AESilky/sd-zid/doc/Timing-TGTGO_to_TGT-switch.pdf

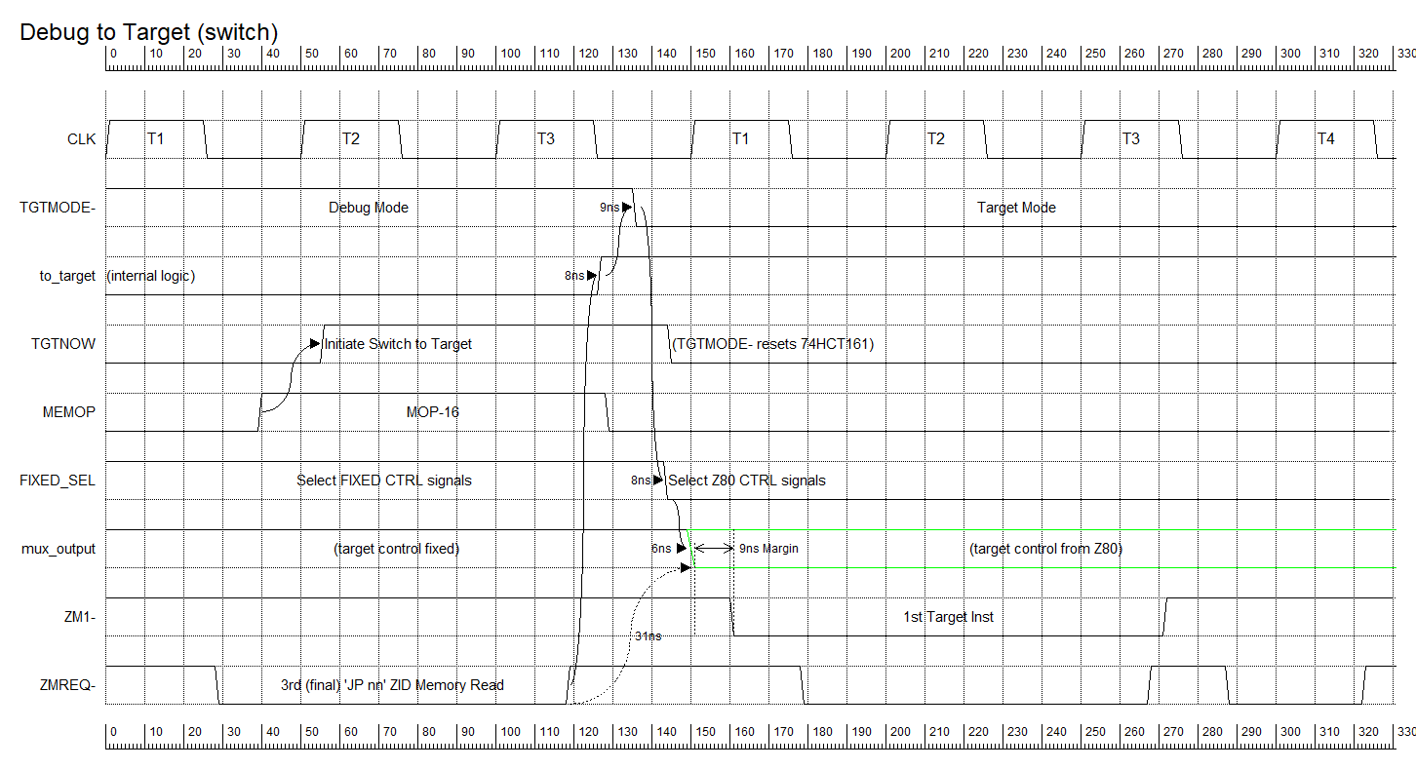
[picture p7: page 1]
