AESilky/sd-zid/doc/Timing-TGTGO_to_TGT-trigger.pdf

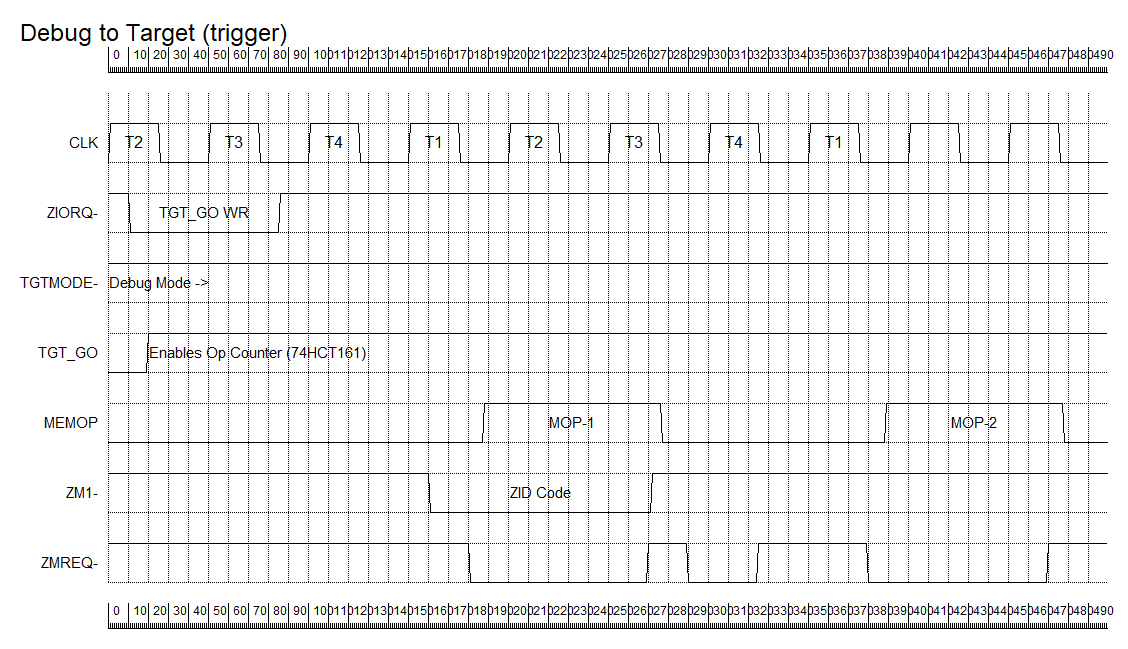
[picture p8: page 1]
