AESilky/sd-zid/doc/ZID-BlockDiag.pdf

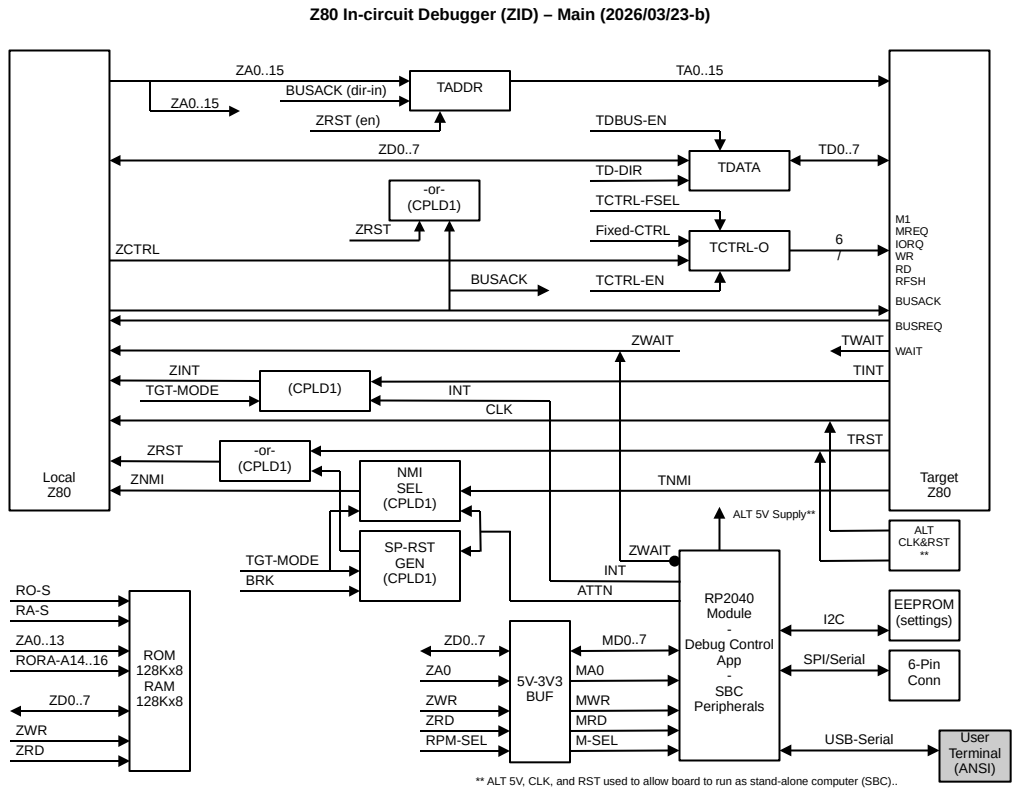
[picture p14: page 1]
User Terminal (ANSI); RP2040 Module - Debug Control App - SBC Peripherals; USB-Serial; EEPROM; (settings); TADDR; TDATA; TCTRL-O; Target Z80; M1 MREQ IORQ WR RD RFSH; Local Z80; SP-RST GEN (CPLD1); NMI SEL (CPLD1); ATTN; ZNMI; TNMI; TRST; -or- (CPLD1); ZRST; (CPLD1); ZINT; TINT; TCTRL-EN; TGT-MODE; ZWAIT; WAIT; RPM-SEL; ALT 5V Supply**; ALT CLK&RST **; BUSACK; BUSREQ; CLK; ROM 128Kx8 RAM; ZA0..13 RORA-A14..16; BRK; Fixed-CTRL; ZCTRL; ZWR ZRD; SPI/Serial; 6-Pin; Conn; INT; TD-DIR; 5V-3V3 BUF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

Z80 In-circuit Debugger (ZID) – Main (2026/03/23-b)

BUSACK (dir-in)

** ALT 5V, CLK, and RST used to allow board to run as stand-alone computer (SBC)..

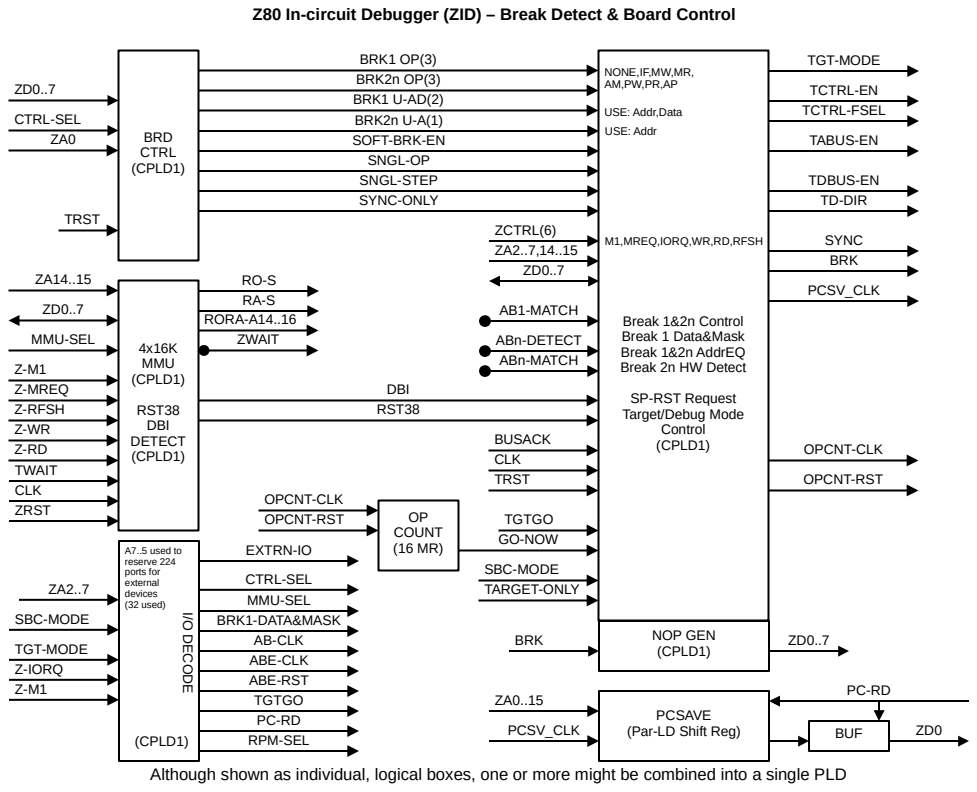
[picture p15: page 2]
ABn-MATCH; BRD CTRL (CPLD1); CTRL-SEL; ZCTRL(6); CLK; OP COUNT (16 MR); TCTRL-FSEL; SYNC; TRST; OPCNT-CLK; OPCNT-RST; OPCNT-CLK OPCNT-RST; GO-NOW; TD-DIR; 4x16K MMU (CPLD1); RST38 DBI DETECT (CPLD1); Z-MREQ; DBI; CLK ZRST; RST38; SBC-MODE; MMU-SEL; BUSACK; TGTGO; ABE-CLK; AB-CLK; ABE-RST TGTGO; Z-IORQ; TGT-MODE; Z-RFSH; RORA-A14..16; BRK; ABn-DETECT; TARGET-ONLY; ZWAIT; NOP GEN (CPLD1); A7..5 used to reserve 224 ports for external devices (32 used); TABUS-EN; TDBUS-EN; PCSV_CLK; AB1-MATCH; BUF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

Z80 In-circuit Debugger (ZID) – Break Detect & Board Control

BRK1 OP(3)
BRK2n OP(3)
BRK1 U-AD(2)
BRK2n U-A(1)
SOFT-BRK-EN
SNGL-OP
SNGL-STEP
SYNC-ONLY

NONE,IF,MW,MR,

USE: Addr,Data
USE: Addr

M1,MREQ,IORQ,WR,RD,RFSH

Break 1&2n Control
Break 1 Data&Mask
Break 1&2n AddrEQ
Break 2n HW Detect

SP-RST Request
Target/Debug Mode
Control
(CPLD1)

RPM-SEL I/O DECODE

PCSAVE
(Par-LD Shift Reg)

Although shown as individual, logical boxes, one or more might be combined into a single PLD

## Break Address Units for

breakpoint-1 and 2-n.

## Target address is shifted into the

AL and AH registers for each unit.

## Address Break Enable is shifted

into ALE and AHE for each unit.

## To detect the number of units present, the Address Break Enables are RESET and a single enable bit is shifted in. After each

2

nd shift, and AB-DETECT is checked. If a unit is detected it is registered and the enable bit is shifted twice, moving it to the next unit. The AB-DETECT is checked again, and if detected, the unit is registered. This process continues until a unit isn’t detected. AB Unit 1 is on the main board, and therefore assumed to exist (no

AB-DETECT needed).

## AB-MATCH and AB-DETECT are Open-Collector outputs to allow all

units to be wire-or’d together.

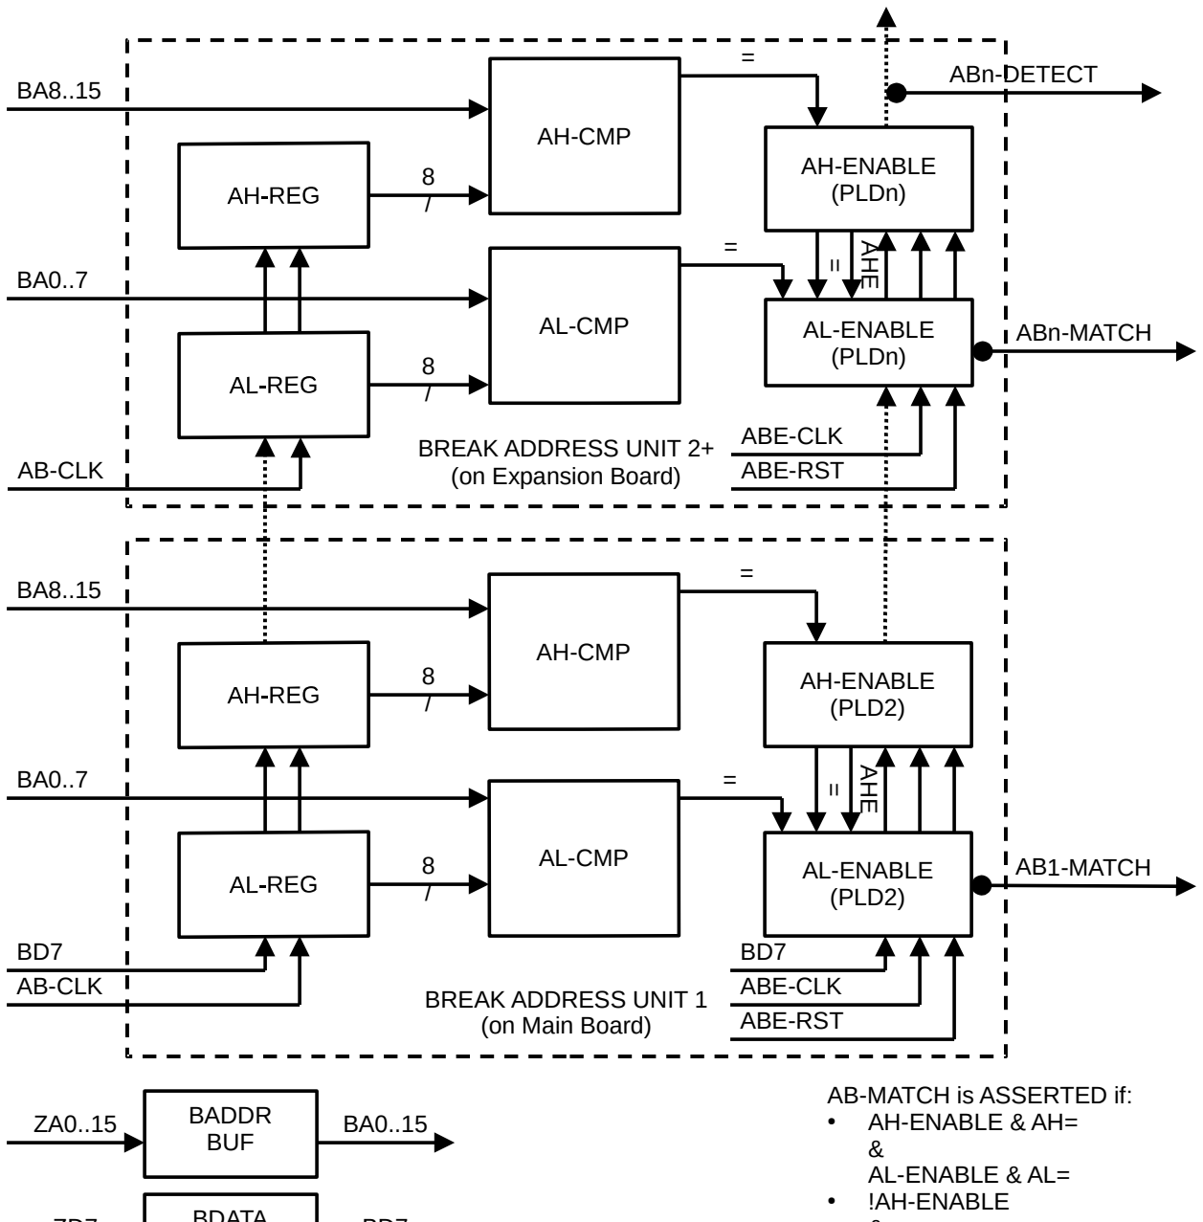
[picture p16: figure]
AL-CMP; AL-ENABLE; (PLD2); BD7 AB-CLK; BD7 ABE-CLK ABE-RST; AH-CMP; AH-ENABLE (PLD2); =AHE; AB1-MATCH; BREAK ADDRESS UNIT 1 (on Main Board); (PLDn) 8 /; AH-ENABLE (PLDn) 8 /; ABn-DETECT; ABn-MATCH; BREAK ADDRESS UNIT 2+ (on Expansion Board); AB-MATCH is ASSERTED if: ● AH-ENABLE & AH= & AL-ENABLE & AL= ● !AH-ENABLE; BA0..15 BADDR BUF; AB-CLK; ABE-CLK ABE-RST

&
AL-ENABLE & AL=

### Z80 In-circuit Debugger (ZID) – Break Address 1 and 2+ Unit(s)

BD7 BDATA
BUF

ZD7
