AESilky/sd-zid/hw/ZID_EXP_BP/schm-plots/ZID_EXP_BP.pdf

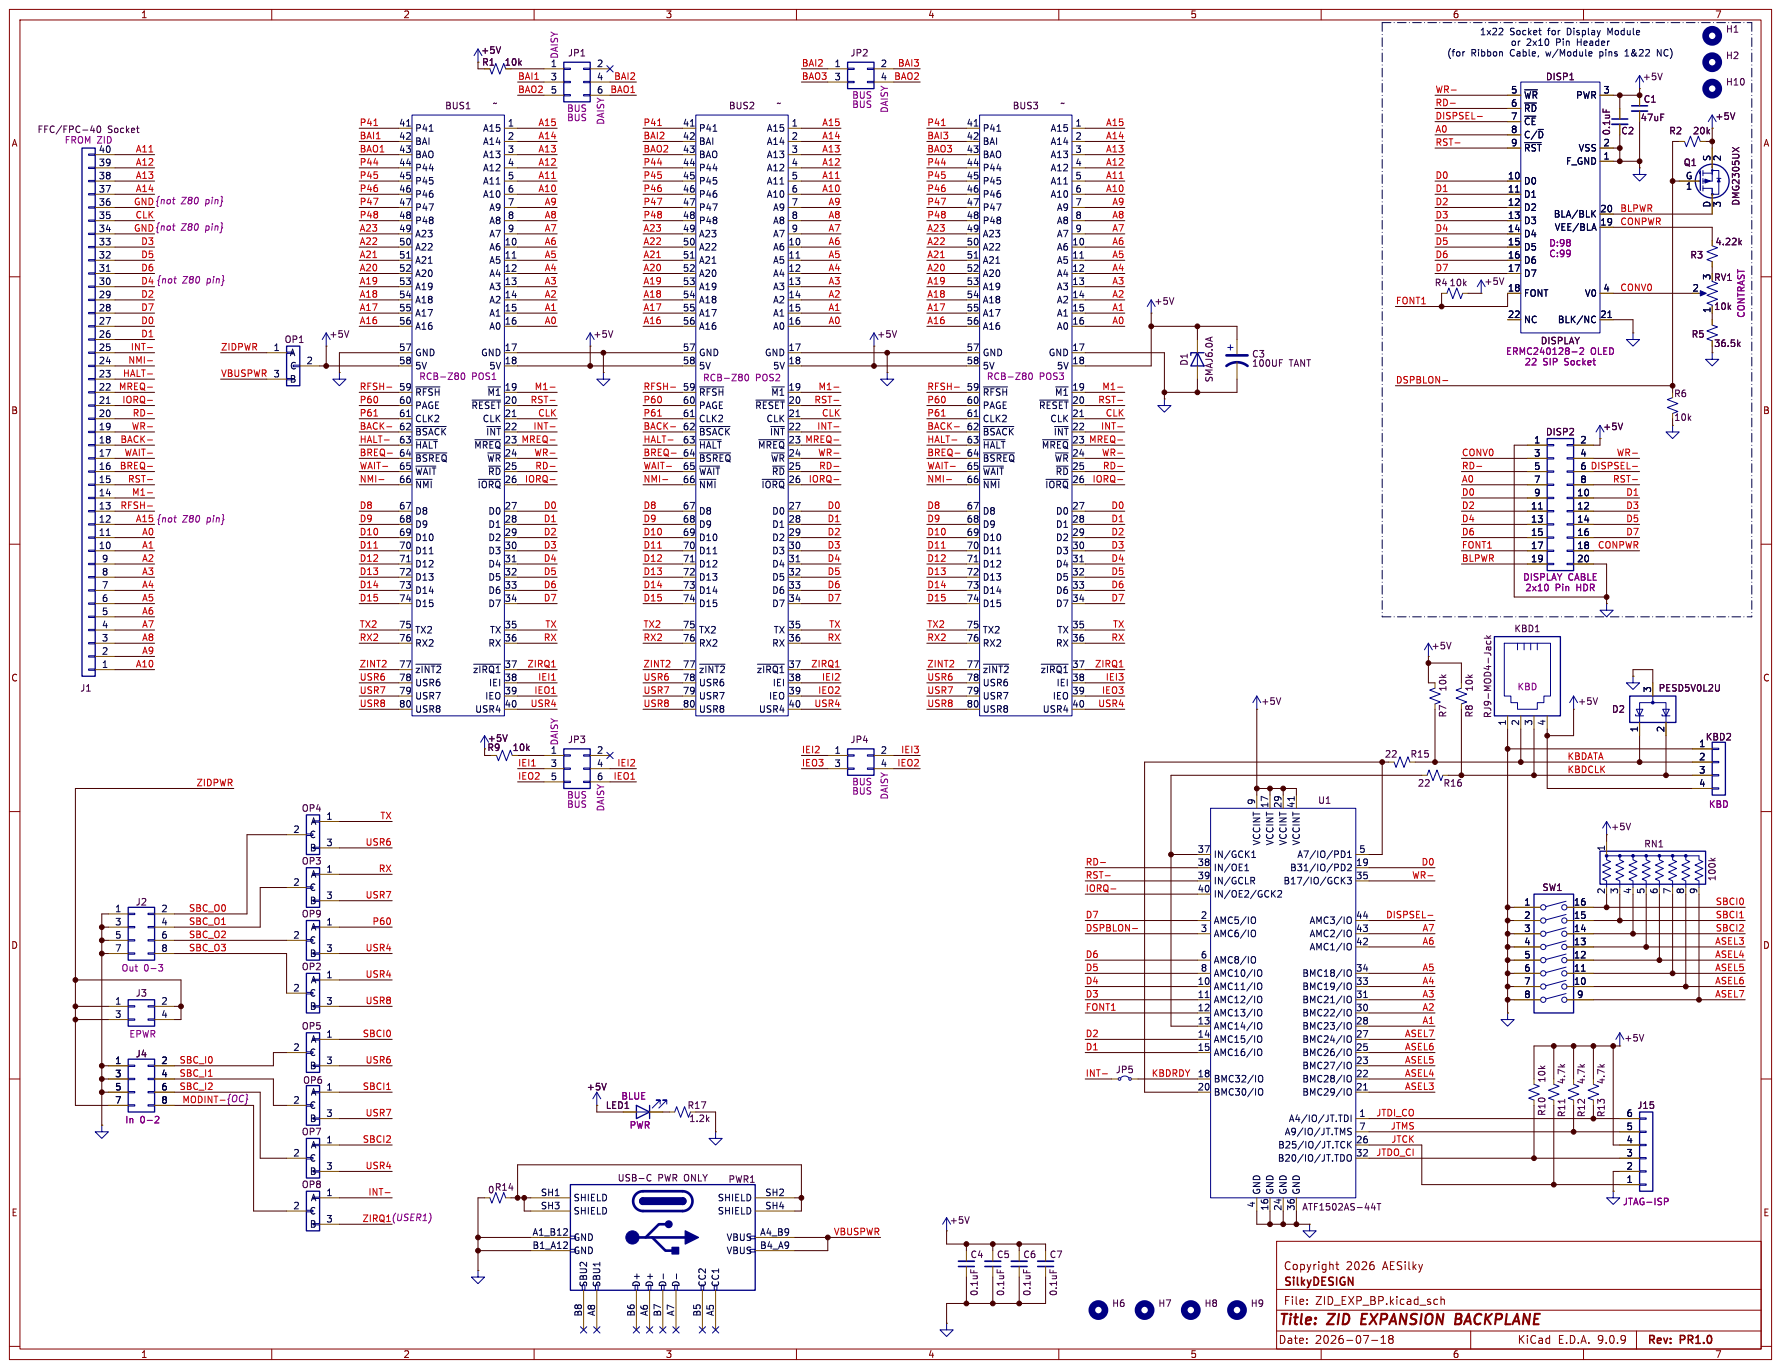
[picture p17: page 1]

1x22 Socket for Display Module
or 2x10 Pin Header
DISP1 DISPLAY

4 VCCINT 17 GND 16 VCCINT 29 GND 24 VCCINT 41 GND 36 A7/IO/PD1 5 B31/IO/PD2 19 B17/IO/GCK3 35 AMC3/IO 44 AMC2/IO 43 AMC1/IO 42 BMC18/IO 34 BMC19/IO 33 BMC21/IO 31 BMC22/IO 30 BMC23/IO 28 BMC24/IO 27 BMC26/IO 25 BMC27/IO 23 BMC28/IO 22 BMC29/IO 21 A4/IO/JT.TDI 1 A9/IO/JT.TMS 7 B25/IO/JT.TCK 26 B20/IO/JT.TDO 32 U1 ATF1502AS-44T 0.1uF C2 C1

A13 GND{not Z80 pin} A14 CLK

5V 58 ~{RFSH} 59 PAGE 60 CLK2 61 ~{BSACK} 62 ~{HALT} 63 ~{BSREQ} 64 ~{WAIT} 65 ~{NMI} 66 D8 67 D9 68 D10 69 D11 70 D12 71 D13 72 D14 73 D15 74 TX2 75 RX2 76 ~{zINT2} 77 USR6 78 USR7 79 USR8 80

5V 18 ~{M1}19 ~{RESET} 20 CLK 21 ~{INT} 22 ~{MREQ} 23 ~{WR} 24 ~{RD} 25 ~{IORQ} 26 D0 27 D1 28 D2 29 D3 30 D4 31 D5 32 D6 33 D7 34 TX 35 RX 36 ~{zIRQ1}37
M1- DSPBLON-
