AESilky/sd-zid/hw/ZID_MAIN/schm-plots/ZID_MAIN.pdf

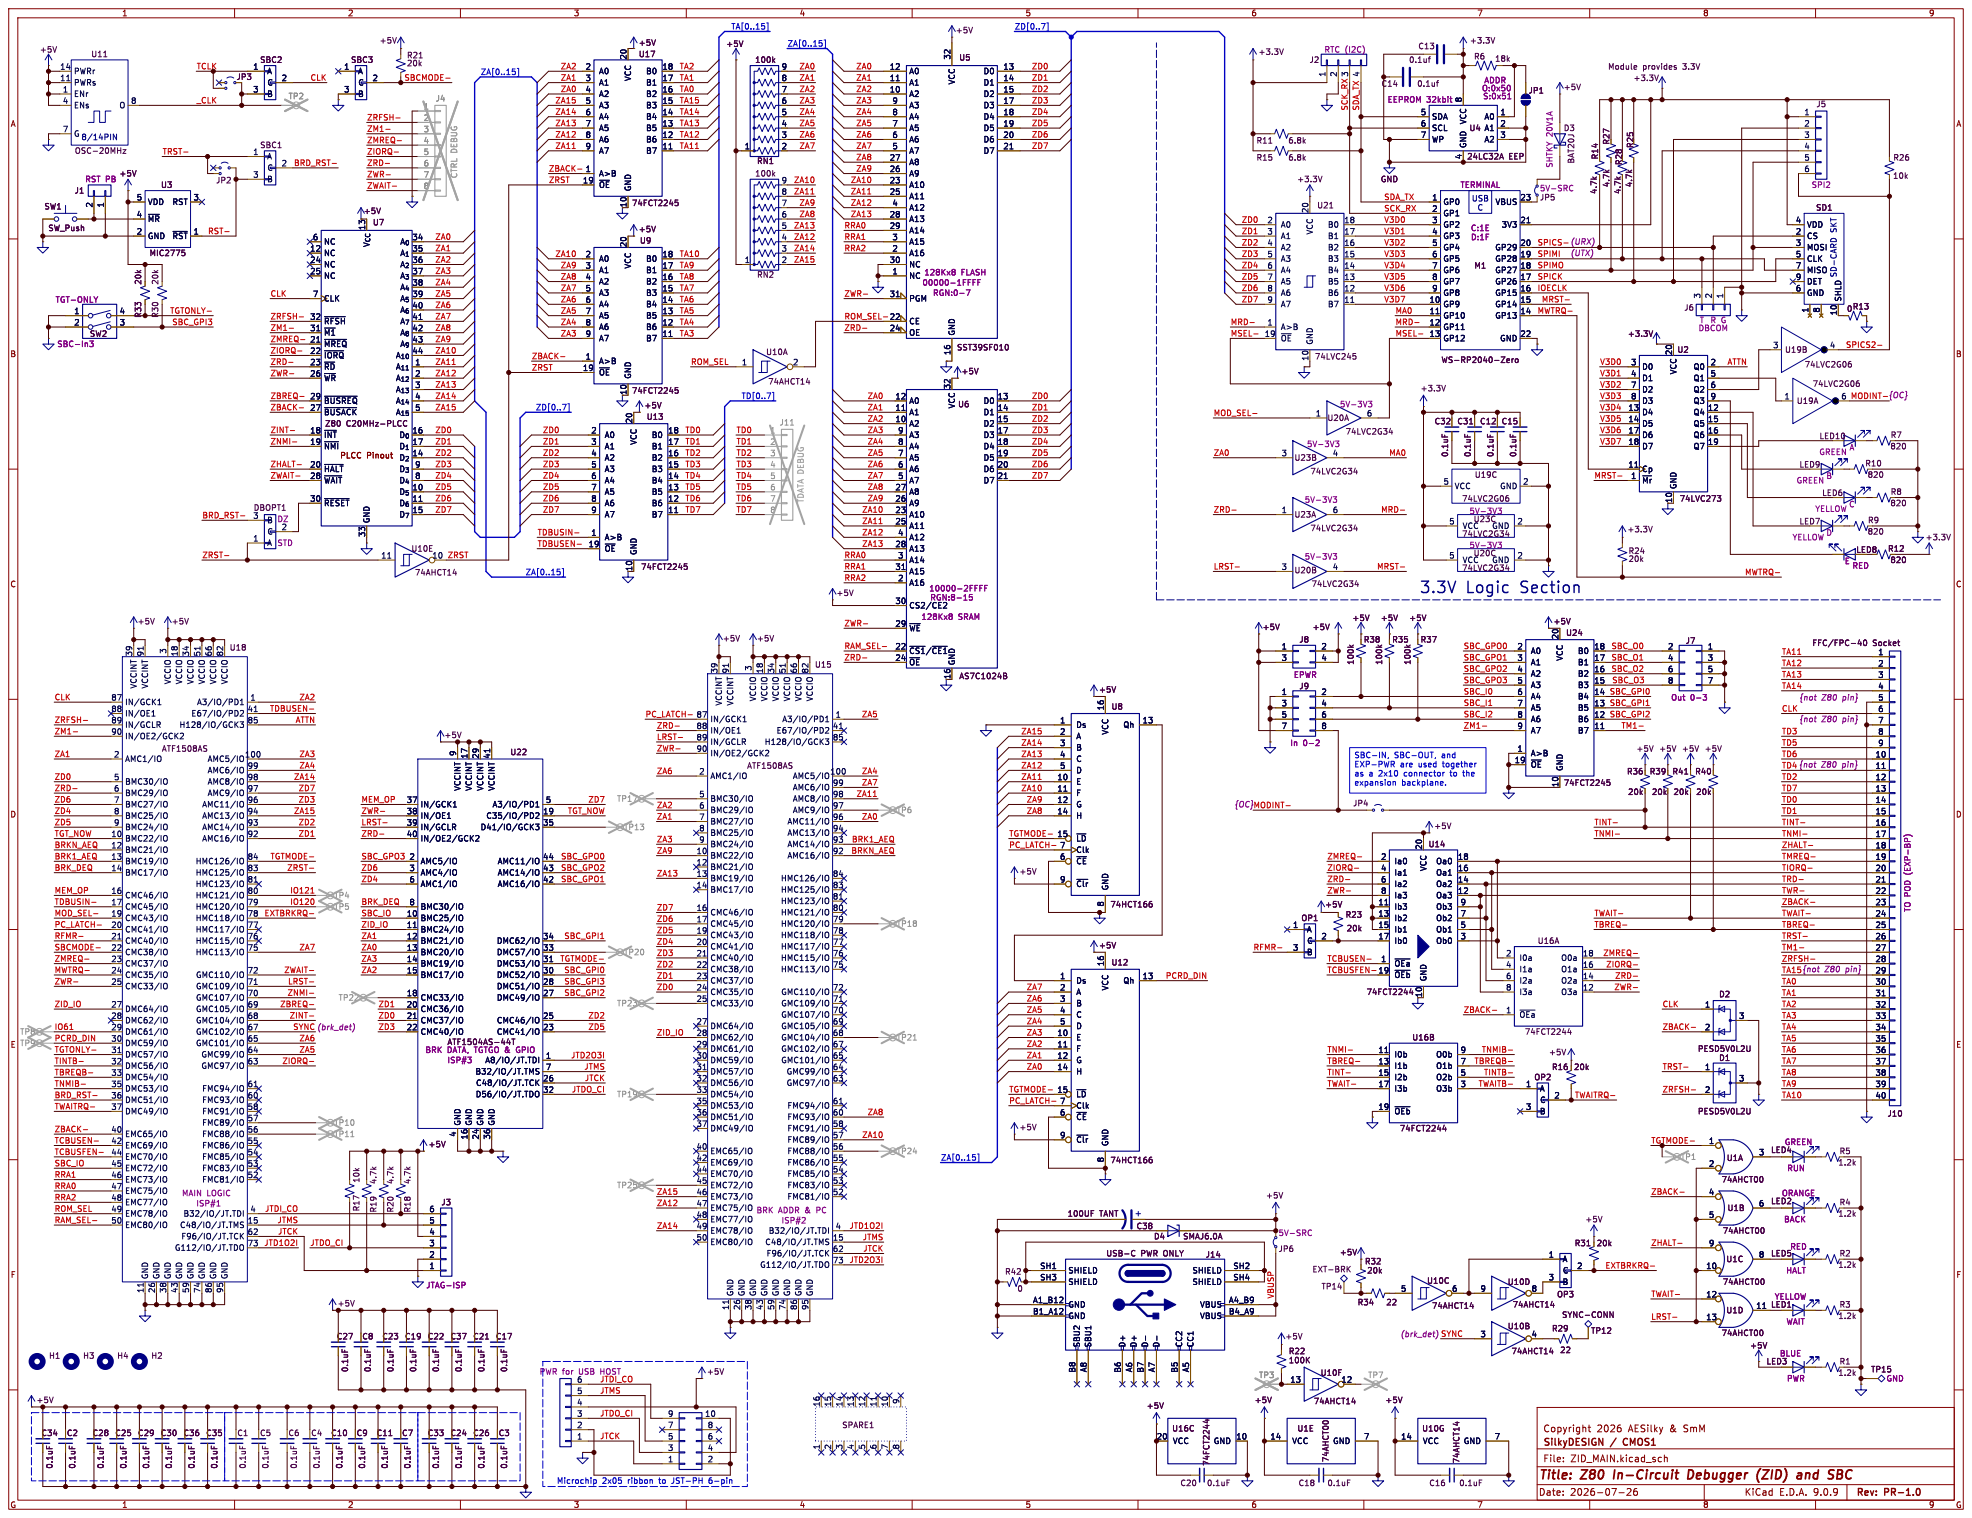
[picture p18: page 1]

Module provides 3.3V 3.3V Logic Section

8 GND
A0 1 A1 2 A2 3 VCC
3V3 21 GP29 20 GP28 19 GP27 18 GP26 17 GP15 16 GP14 15 GP13 14 GND 22 M1 WS-RP2040-Zero TERMINAL C:1E D:1F

4 SDA 5 SCL 6 WP 7 R28 4.7k R25 4.7k R13 0 SD1 VDD

8 SHLD 10 +3.3V M1 WS-RP2040-Zero TERMINAL C:1E D:1F GP0 1 GP1 2 GP2 3 GP3 4 GP4 5 GP5 6 GP6 7 GP7 8 GP8 9 GP9 10 GP10 11 GP11 12 GP12 13 VBUS 23

3 GND 38 VCCIO 18 GND 43 VCCIO 34 GND 59 VCCIO 51 GND 74 VCCIO 66 GND 86 VCCIO 82 GND 95 A3/IO/PD1 1 E67/IO/PD2 41 H128/IO/GCK3 85 AMC5/IO 100 AMC6/IO 99 AMC8/IO 98 AMC9/IO 97 AMC11/IO 96 AMC13/IO 94 AMC14/IO 93 AMC16/IO 92 HMC126/IO 84 HMC125/IO 83 HMC123/IO 81 HMC121/IO 80 HMC120/IO 79 HMC118/IO 78 HMC117/IO 77 HMC115/IO 76 HMC113/IO 75 GMC110/IO 72 GMC109/IO 71 GMC107/IO 70 GMC105/IO 69 GMC104/IO 68 GMC102/IO 67 GMC101/IO 65 GMC99/IO 64 GMC97/IO 63 FMC94/IO 61 FMC93/IO 60 FMC91/IO 58 FMC89/IO 57 FMC88/IO 56 FMC86/IO 55 FMC85/IO 54 FMC83/IO 53 FMC81/IO 52 B32/IO/JT.TDI 4 C48/IO/JT.TMS 15 F96/IO/JT.TCK 62 G112/IO/JT.TDO 73

4 VCCINT 17 GND 16 VCCINT 29 GND 24 VCCINT 41 GND 36 A3/IO/PD1 5 C35/IO/PD2 19 D41/IO/GCK3 35 AMC11/IO 44 AMC14/IO 43 AMC16/IO 42 DMC62/IO 34 DMC57/IO 33 DMC53/IO 31 DMC52/IO 30 DMC51/IO 28 DMC49/IO 27 CMC46/IO 25 CMC41/IO 23 A8/IO/JT.TDI 1 B32/IO/JT.TMS 7 C48/IO/JT.TCK 26 D56/IO/JT.TDO 32 U22 ATF1504AS-44T BRK DATA, TGTGO & GPIO

4 VCCINT 17 GND 16 VCCINT 29 GND 24 VCCINT 41 GND 36 A3/IO/PD1 5 C35/IO/PD2 19 D41/IO/GCK3 35 AMC11/IO 44 AMC14/IO 43 AMC16/IO 42 DMC62/IO 34 DMC57/IO 33 DMC53/IO 31 DMC52/IO 30 DMC51/IO 28 DMC49/IO 27 CMC46/IO 25 CMC41/IO 23 A8/IO/JT.TDI 1 B32/IO/JT.TMS 7 C48/IO/JT.TCK 26 D56/IO/JT.TDO 32 R36

6 PWR for USB HOST
