AESilky/sd-zid/hw/ZID_EXP_BP/comp-docs/Modular_4_Jack-fci-68897-001lf.pdf

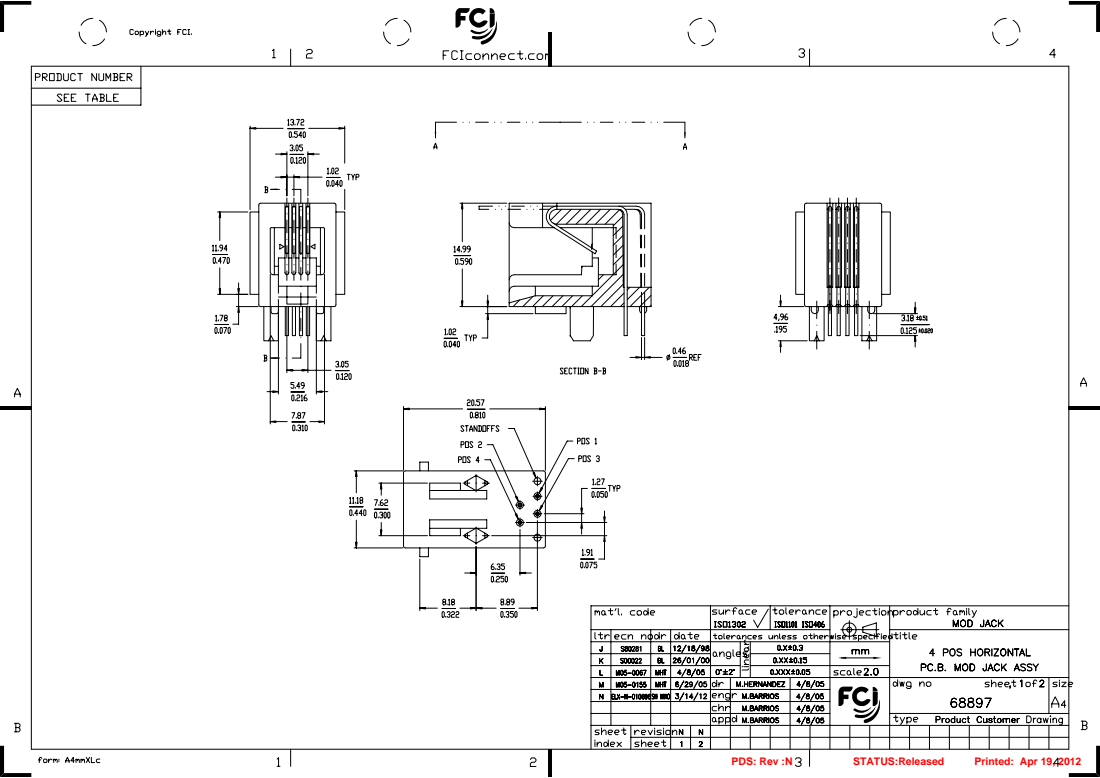
[picture p19: page 1]
PDS: Rev :N; STATUS:Released; Printed: Apr 19, 2012

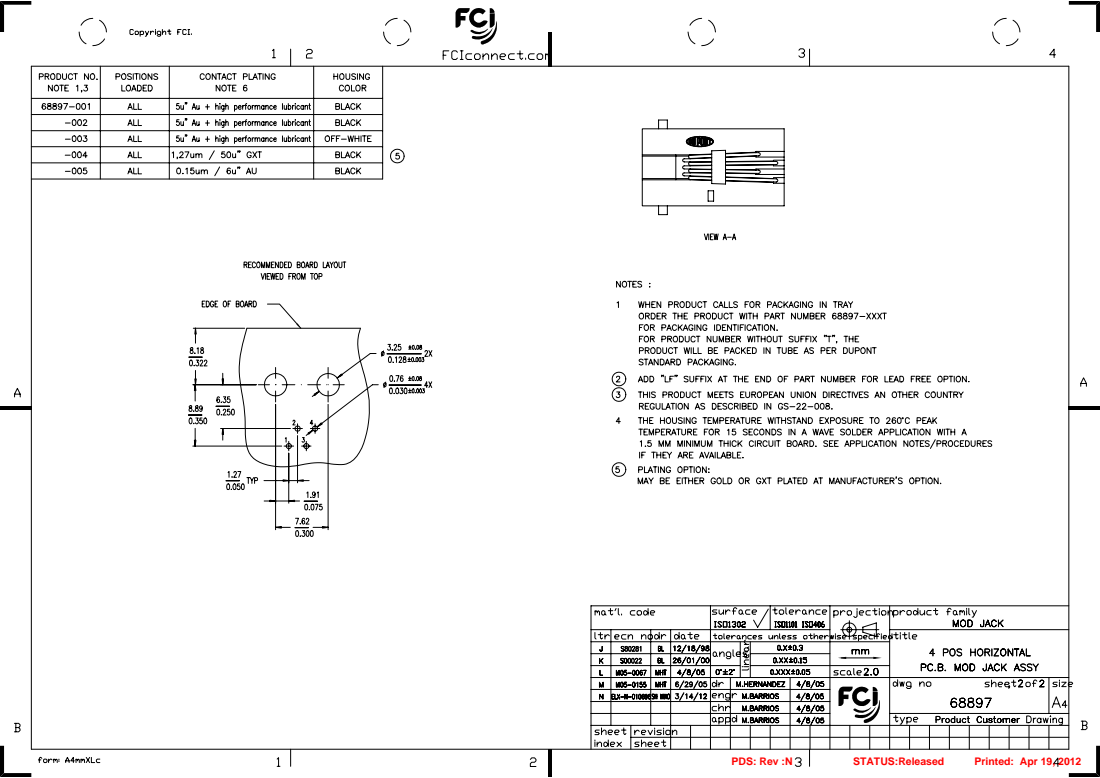
[picture p20: page 2]
PDS: Rev :N; STATUS:Released; Printed: Apr 19, 2012
