AESilky/sd-zid/hw/ZID_BRK_EXP/schm_plots/ZID_BRK_EXP.pdf

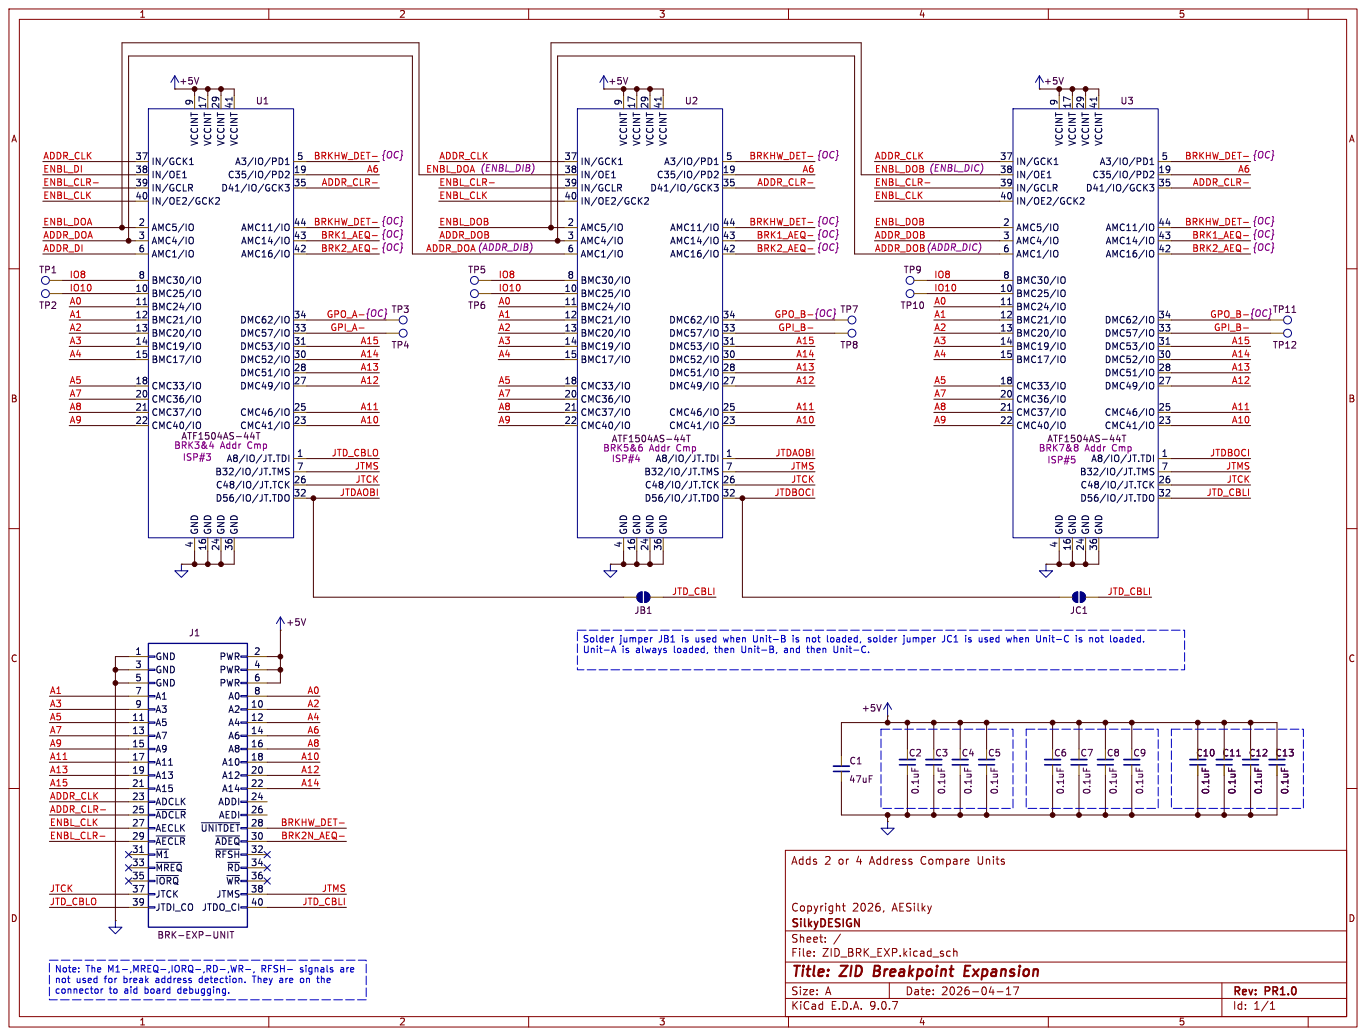
[picture p21: page 1]

4 VCCINT 17 GND 16 VCCINT 29 GND 24 VCCINT 41 GND 36 A3/IO/PD1 5 C35/IO/PD2 19 D41/IO/GCK3 35 AMC11/IO 44 AMC14/IO 43 AMC16/IO 42 DMC62/IO 34 DMC57/IO 33 DMC53/IO 31 DMC52/IO 30 DMC51/IO 28 DMC49/IO 27 CMC46/IO 25 CMC41/IO 23 A8/IO/JT.TDI 1 B32/IO/JT.TMS 7 C48/IO/JT.TCK 26 D56/IO/JT.TDO 32 U1 ATF1504AS-44T BRK3&4 Addr Cmp

4 VCCINT 17 GND 16 VCCINT 29 GND 24 VCCINT 41 GND 36 A3/IO/PD1 5 C35/IO/PD2 19 D41/IO/GCK3 35 AMC11/IO 44 AMC14/IO 43 AMC16/IO 42 DMC62/IO 34 DMC57/IO 33 DMC53/IO 31 DMC52/IO 30 DMC51/IO 28 DMC49/IO 27 CMC46/IO 25 CMC41/IO 23 A8/IO/JT.TDI 1 B32/IO/JT.TMS 7 C48/IO/JT.TCK 26 D56/IO/JT.TDO 32 U2 ATF1504AS-44T BRK5&6 Addr Cmp

4 VCCINT 17 GND 16 VCCINT 29 GND 24 VCCINT 41 GND 36 A3/IO/PD1 5 C35/IO/PD2 19 D41/IO/GCK3 35 AMC11/IO 44 AMC14/IO 43 AMC16/IO 42 DMC62/IO 34 DMC57/IO 33 DMC53/IO 31 DMC52/IO 30 DMC51/IO 28 DMC49/IO 27 CMC46/IO 25 CMC41/IO 23 A8/IO/JT.TDI 1 B32/IO/JT.TMS 7 C48/IO/JT.TCK 26 D56/IO/JT.TDO 32 U3 ATF1504AS-44T BRK7&8 Addr Cmp

Id: 1/1 Title: ZID Breakpoint Expansion
