AESilky/sd-zid/hw/ZID_POD/Pod1/schm-plots/ZID_POD.pdf

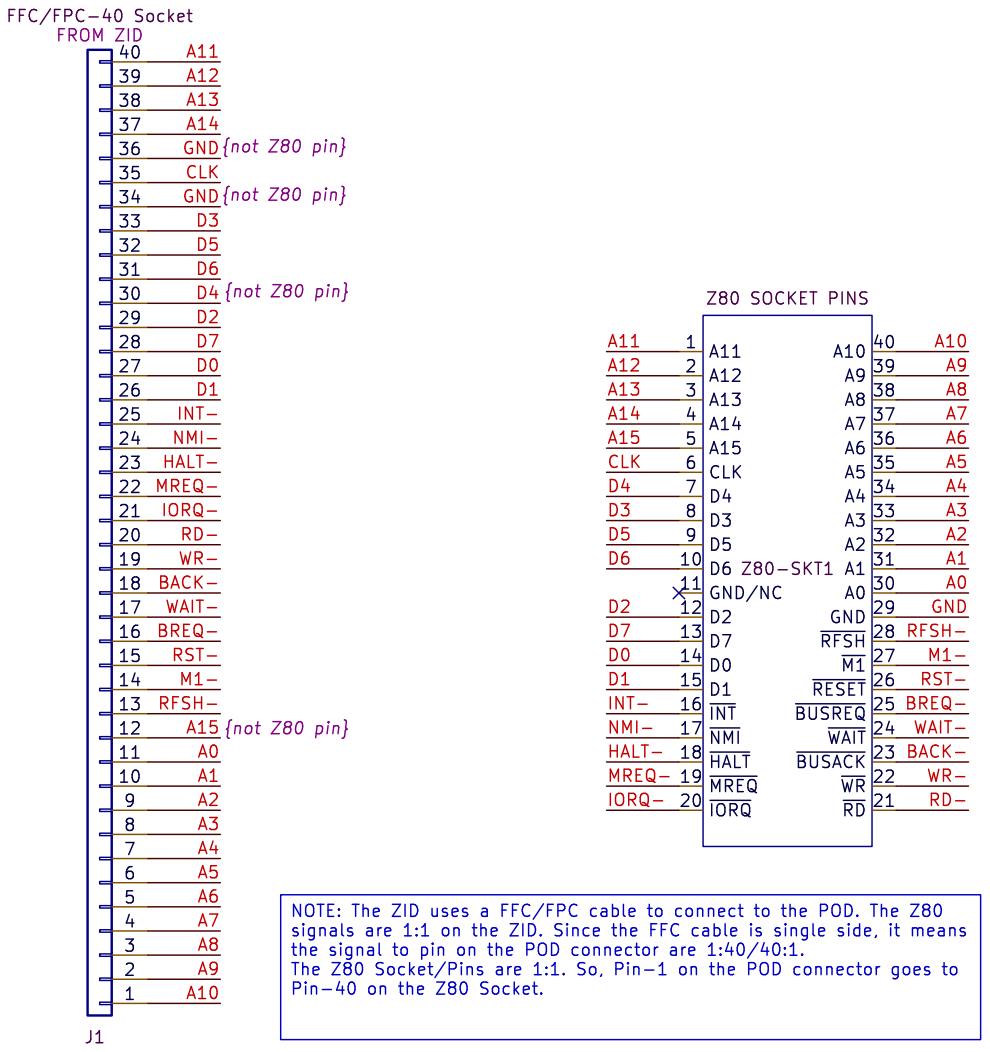
[picture p22: page 1]

INT- MREQ- HALT- NMI- A2A0 A15 {not Z80 pin} A1 A10A7A9A6 RD-A8A4A3 GND{not Z80 pin} CLK

signals are 1:1 on the ZID. Since the FFC cable is single side, it means

Id: 1/1 Title: ZID POD (1) File: ZID_POD.kicad_sch Sheet: / SilkyDESIGN
