AESilky/sd-zid/hw/prod-doc/plcc_44_at_socket.pdf

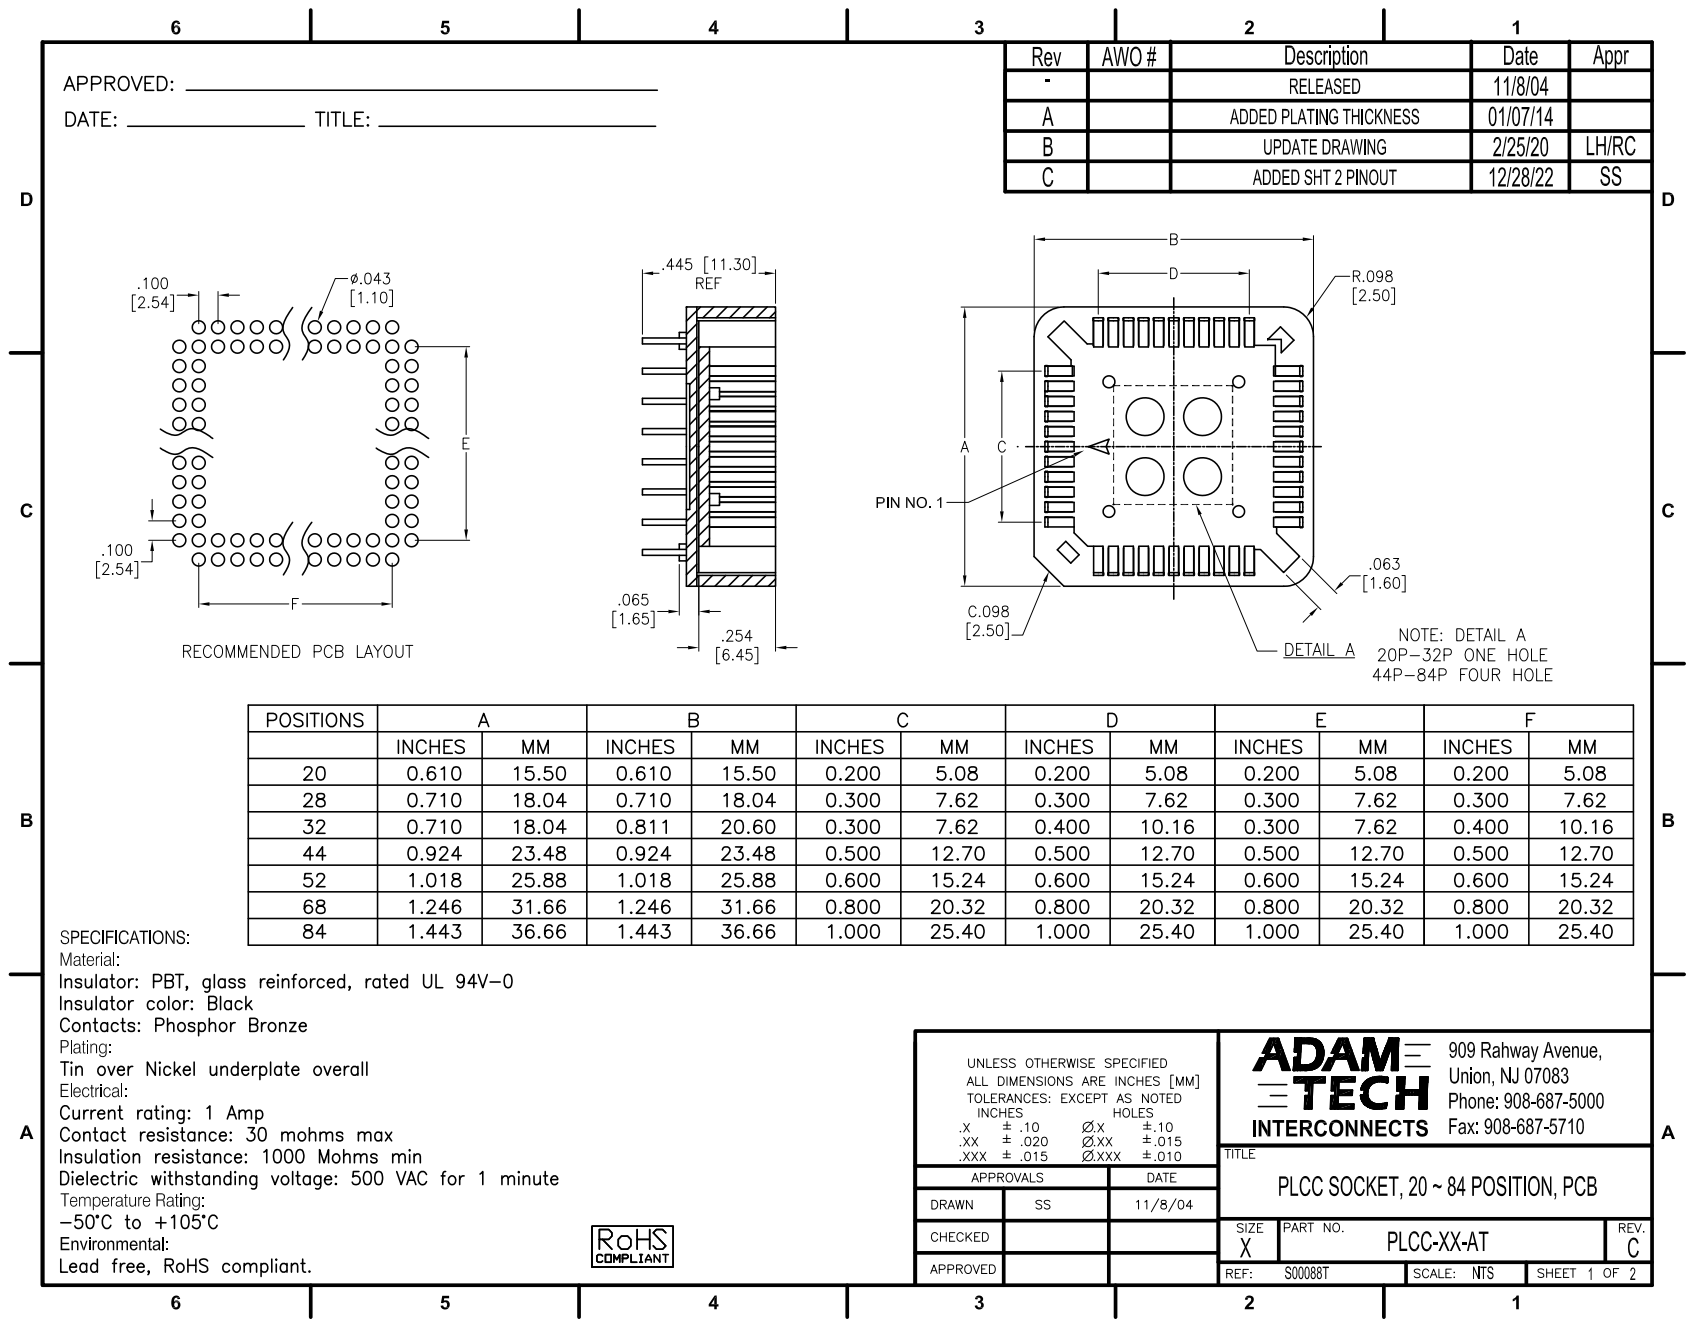
[picture p28: page 1]

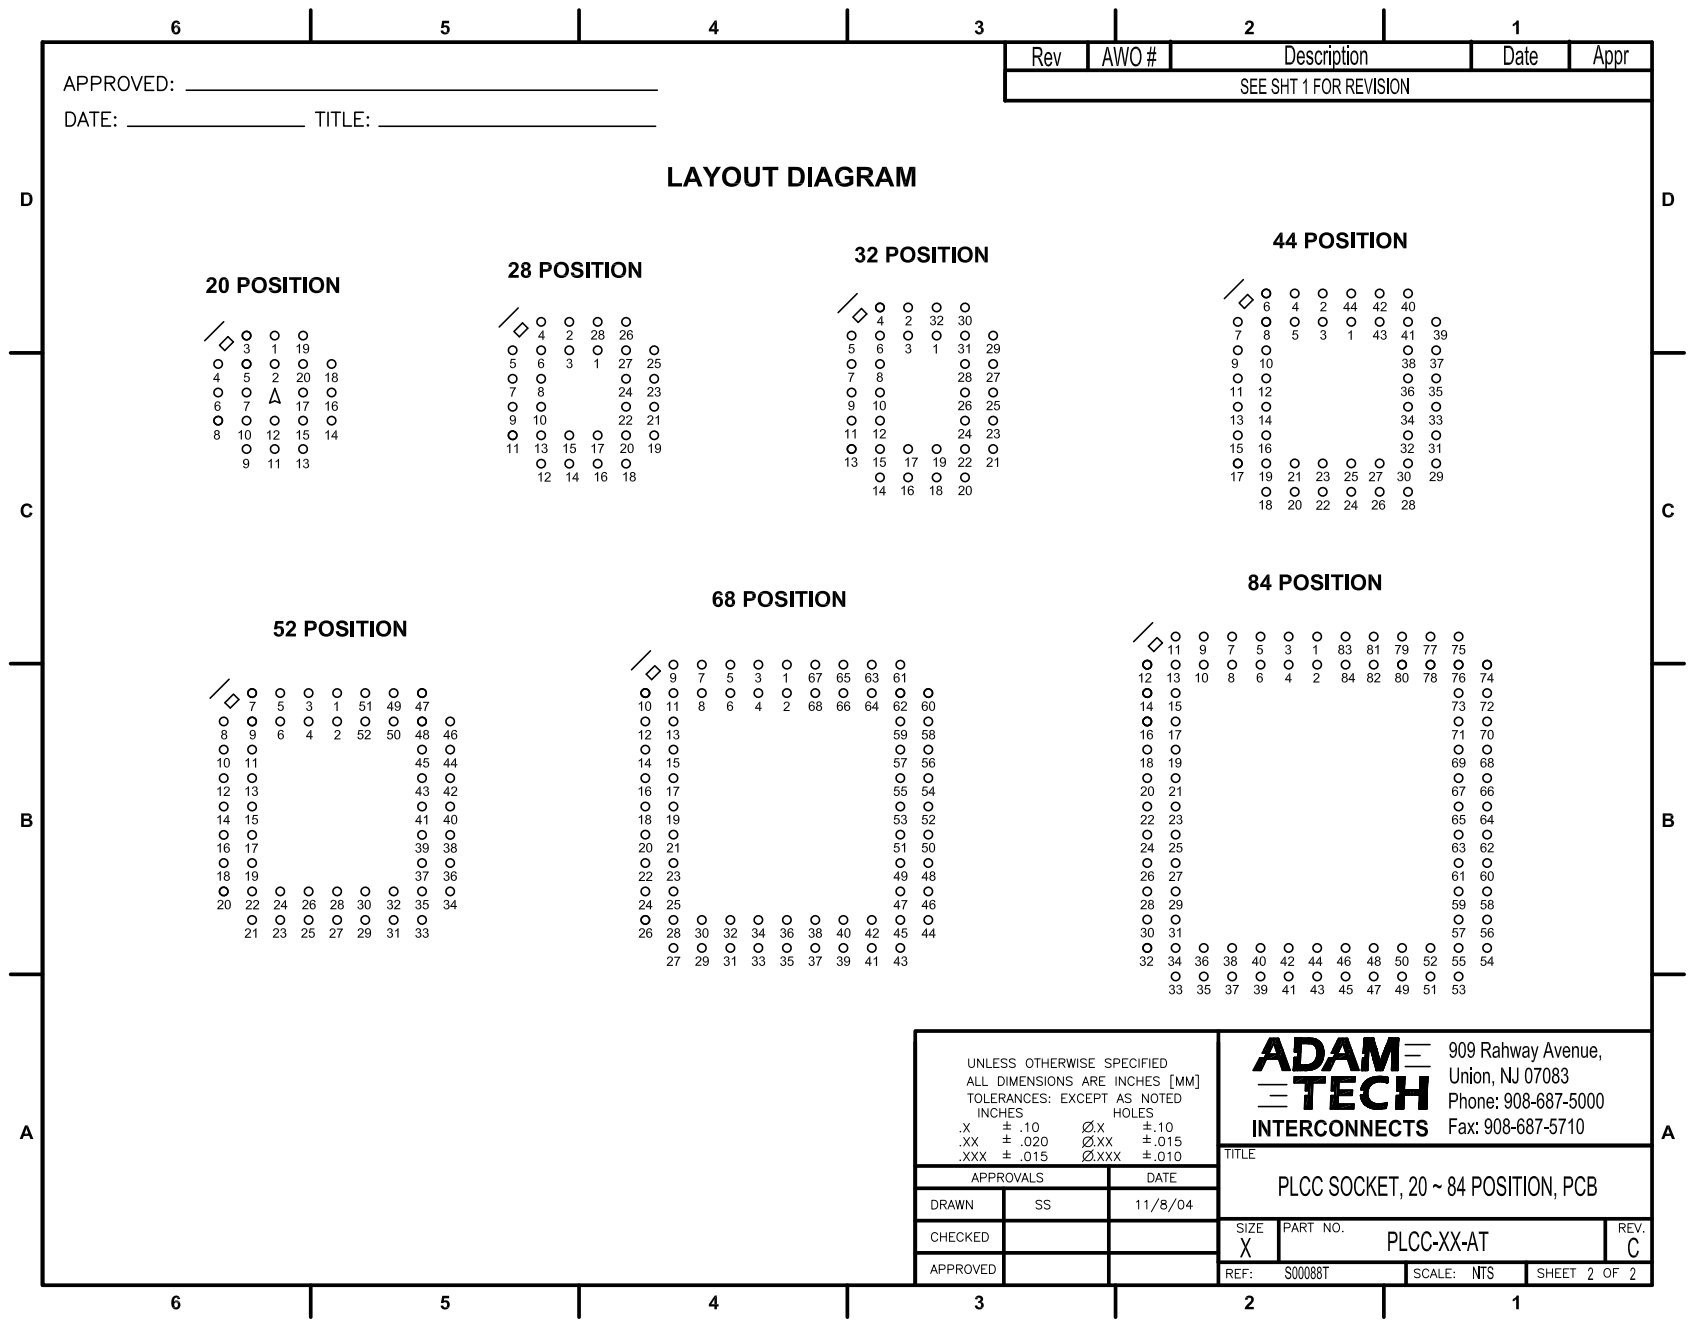
[picture p29: page 2]
