AESilky/sd-zid/hw/prod-doc/FPC-V-Conn-CviLux_CF2081S.pdf

# CviLux

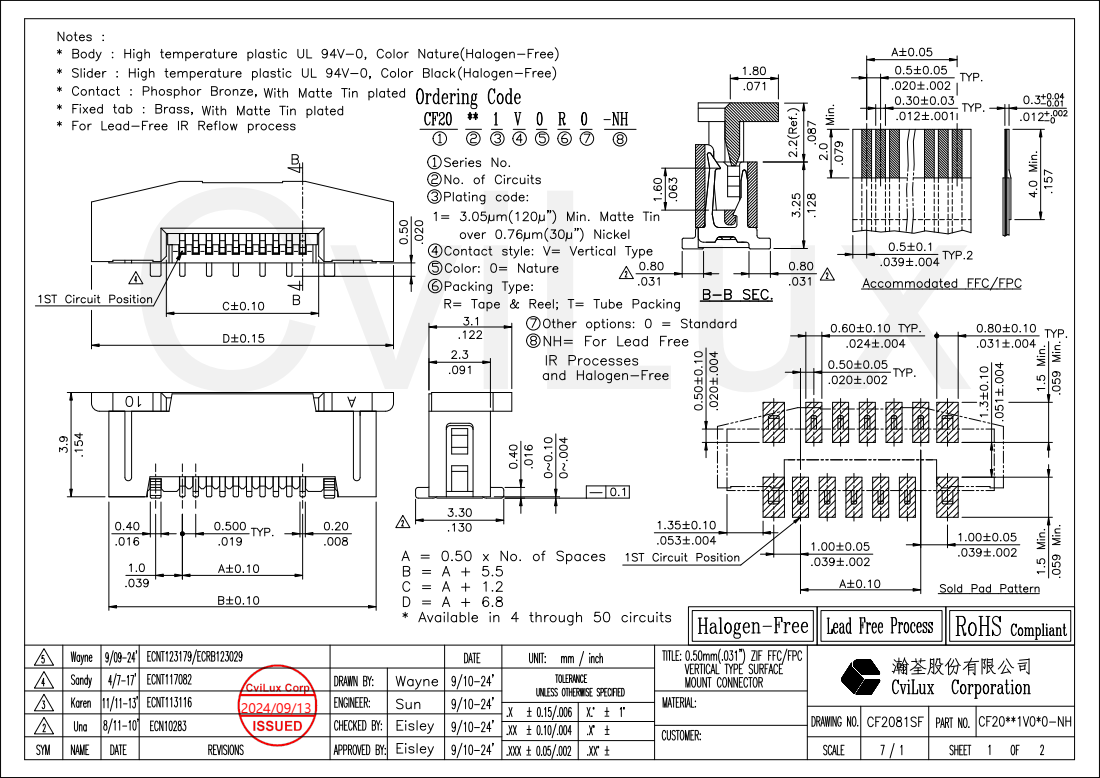
[picture p30: page 1]

# CviLux

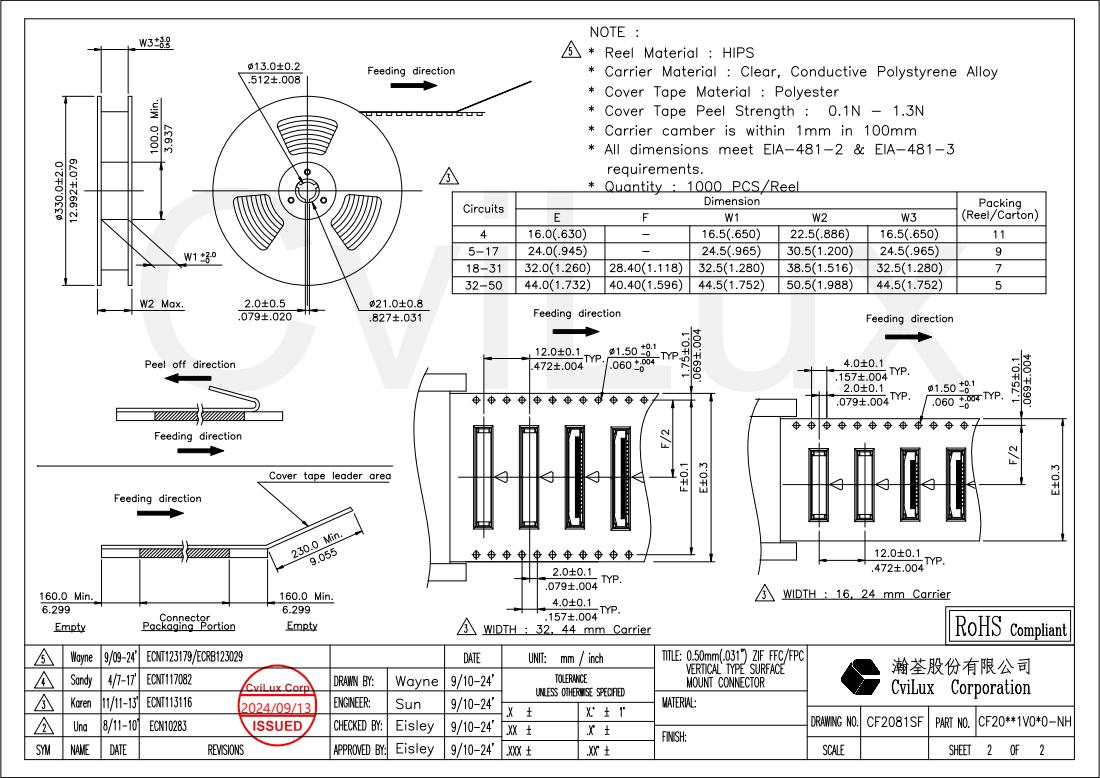
[picture p31: page 2]
