AESilky/sd-zid/hw/prod-doc/FPC-Conn-CviLux_CF2520S.pdf

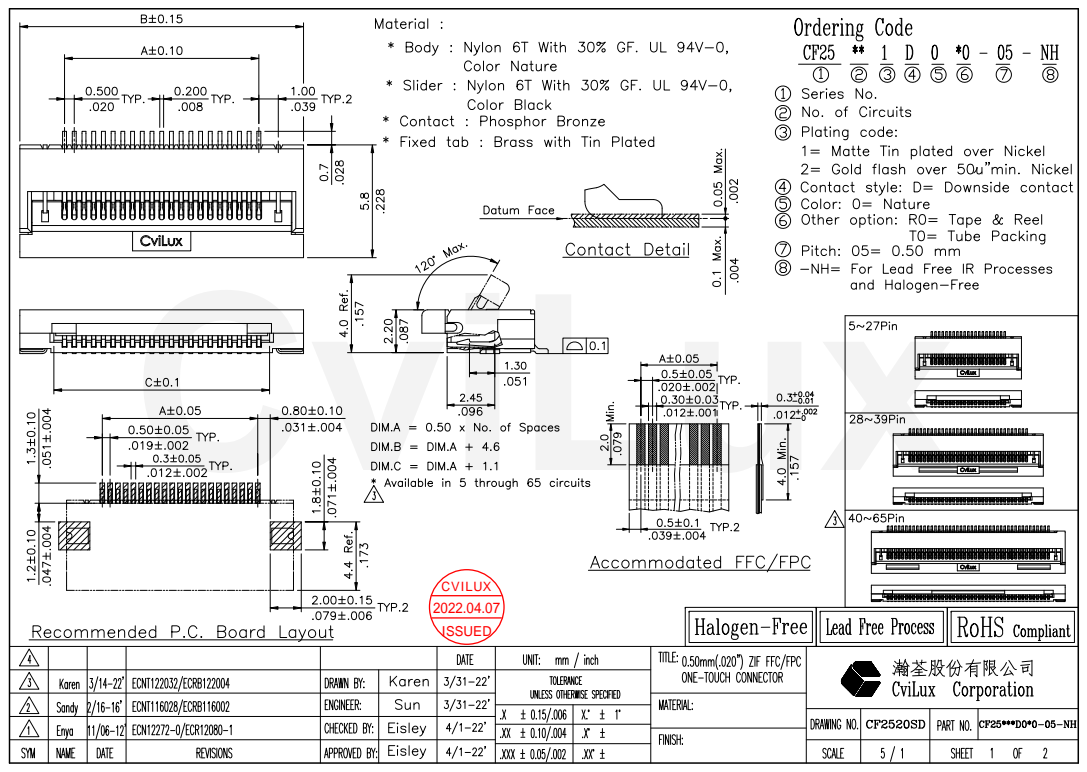
[picture p32: page 1]
CviLux

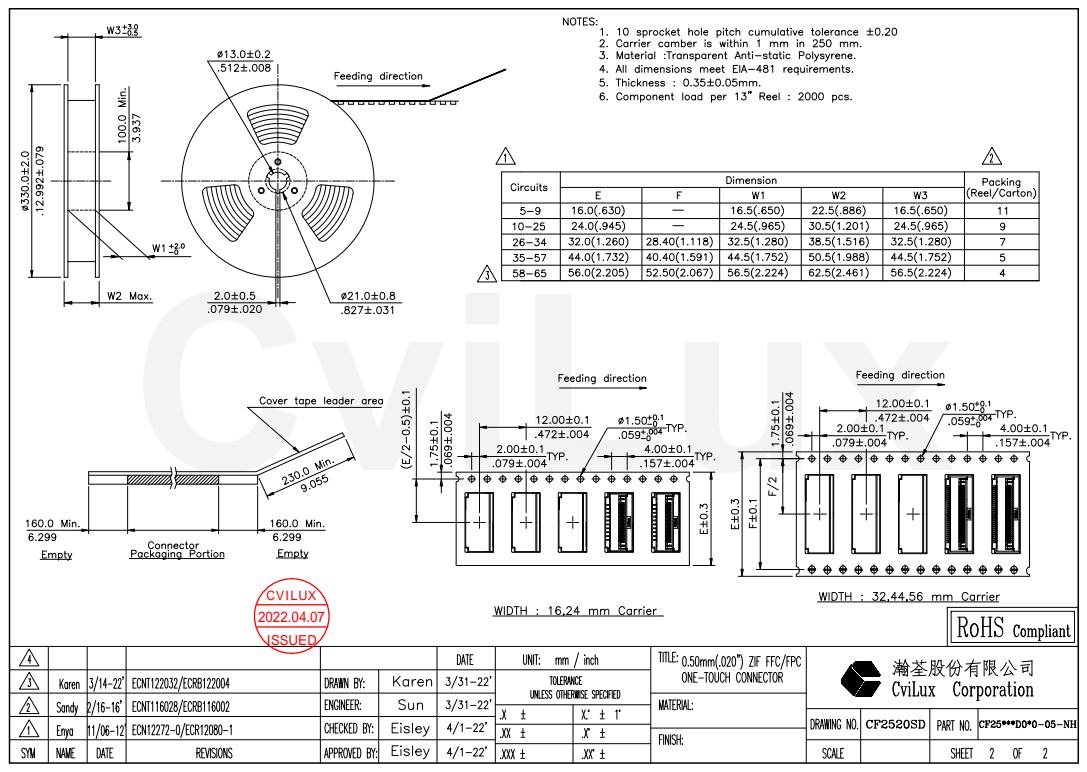
[picture p33: page 2]
CviLux
