AESilky/sd-zid/hw/history/v0_1/sd-zicd.kicad_sch

## KiCad design hw/history/v0_1/sd-zicd.kicad_sch (2026-02-24)

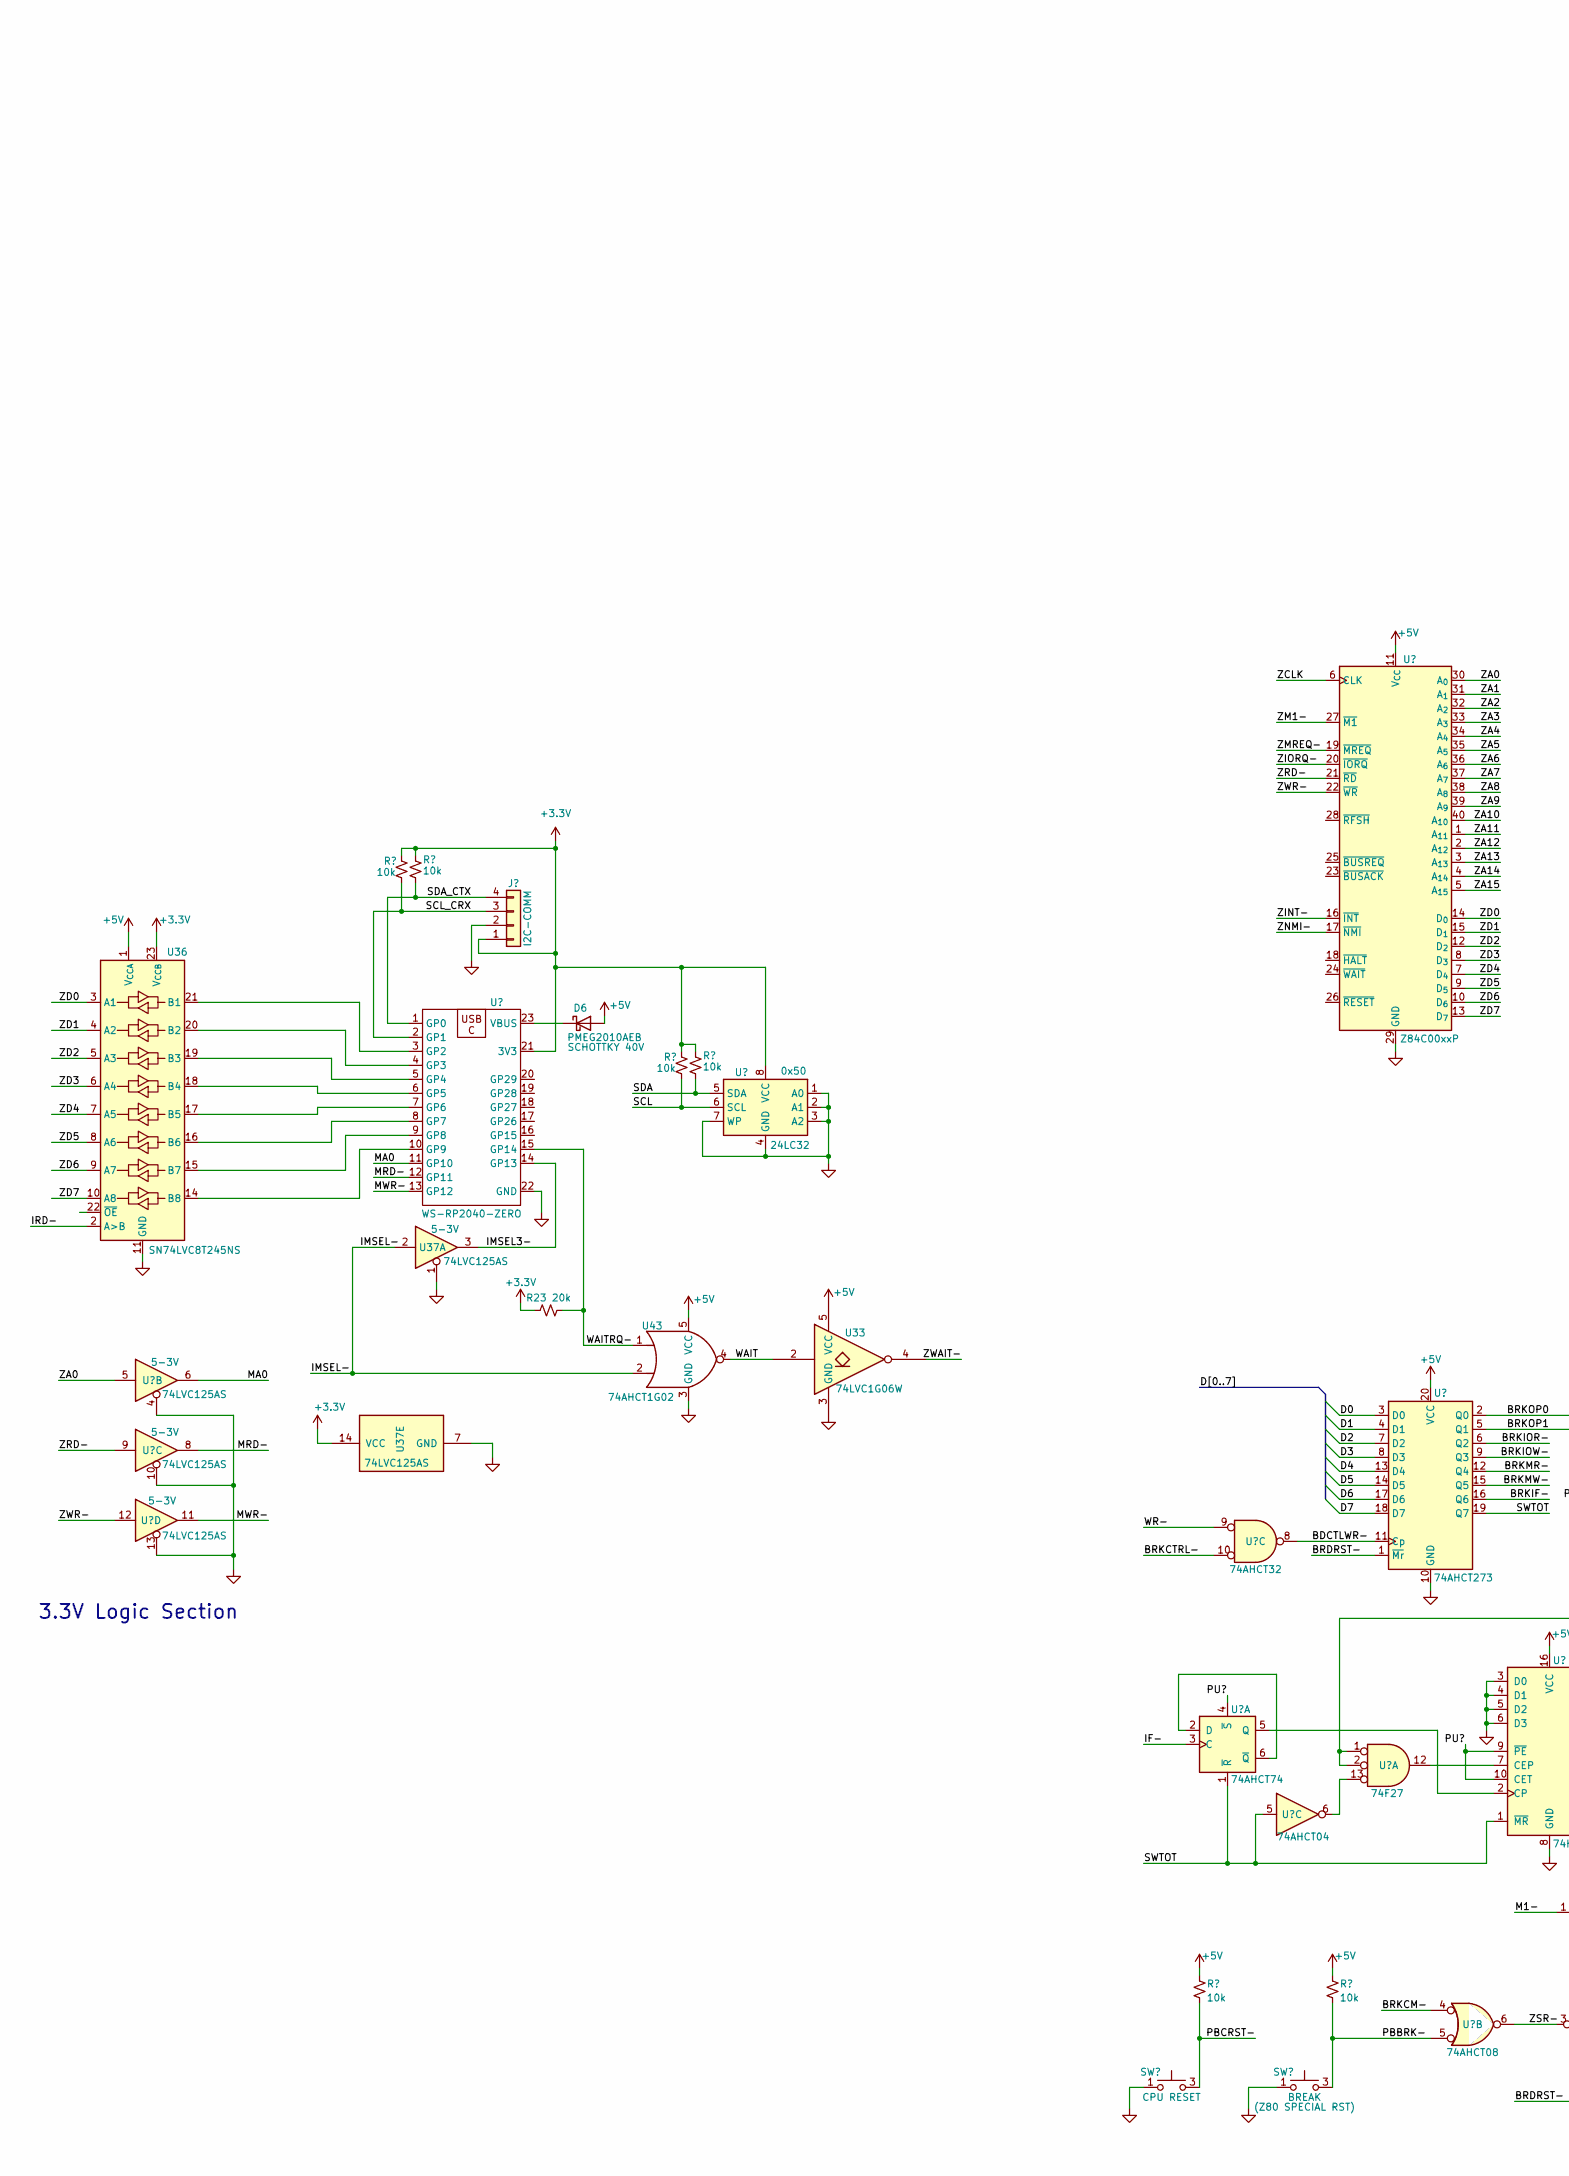
[picture p40: schematic sd-zicd.kicad_sch, part in row 1, column 1]

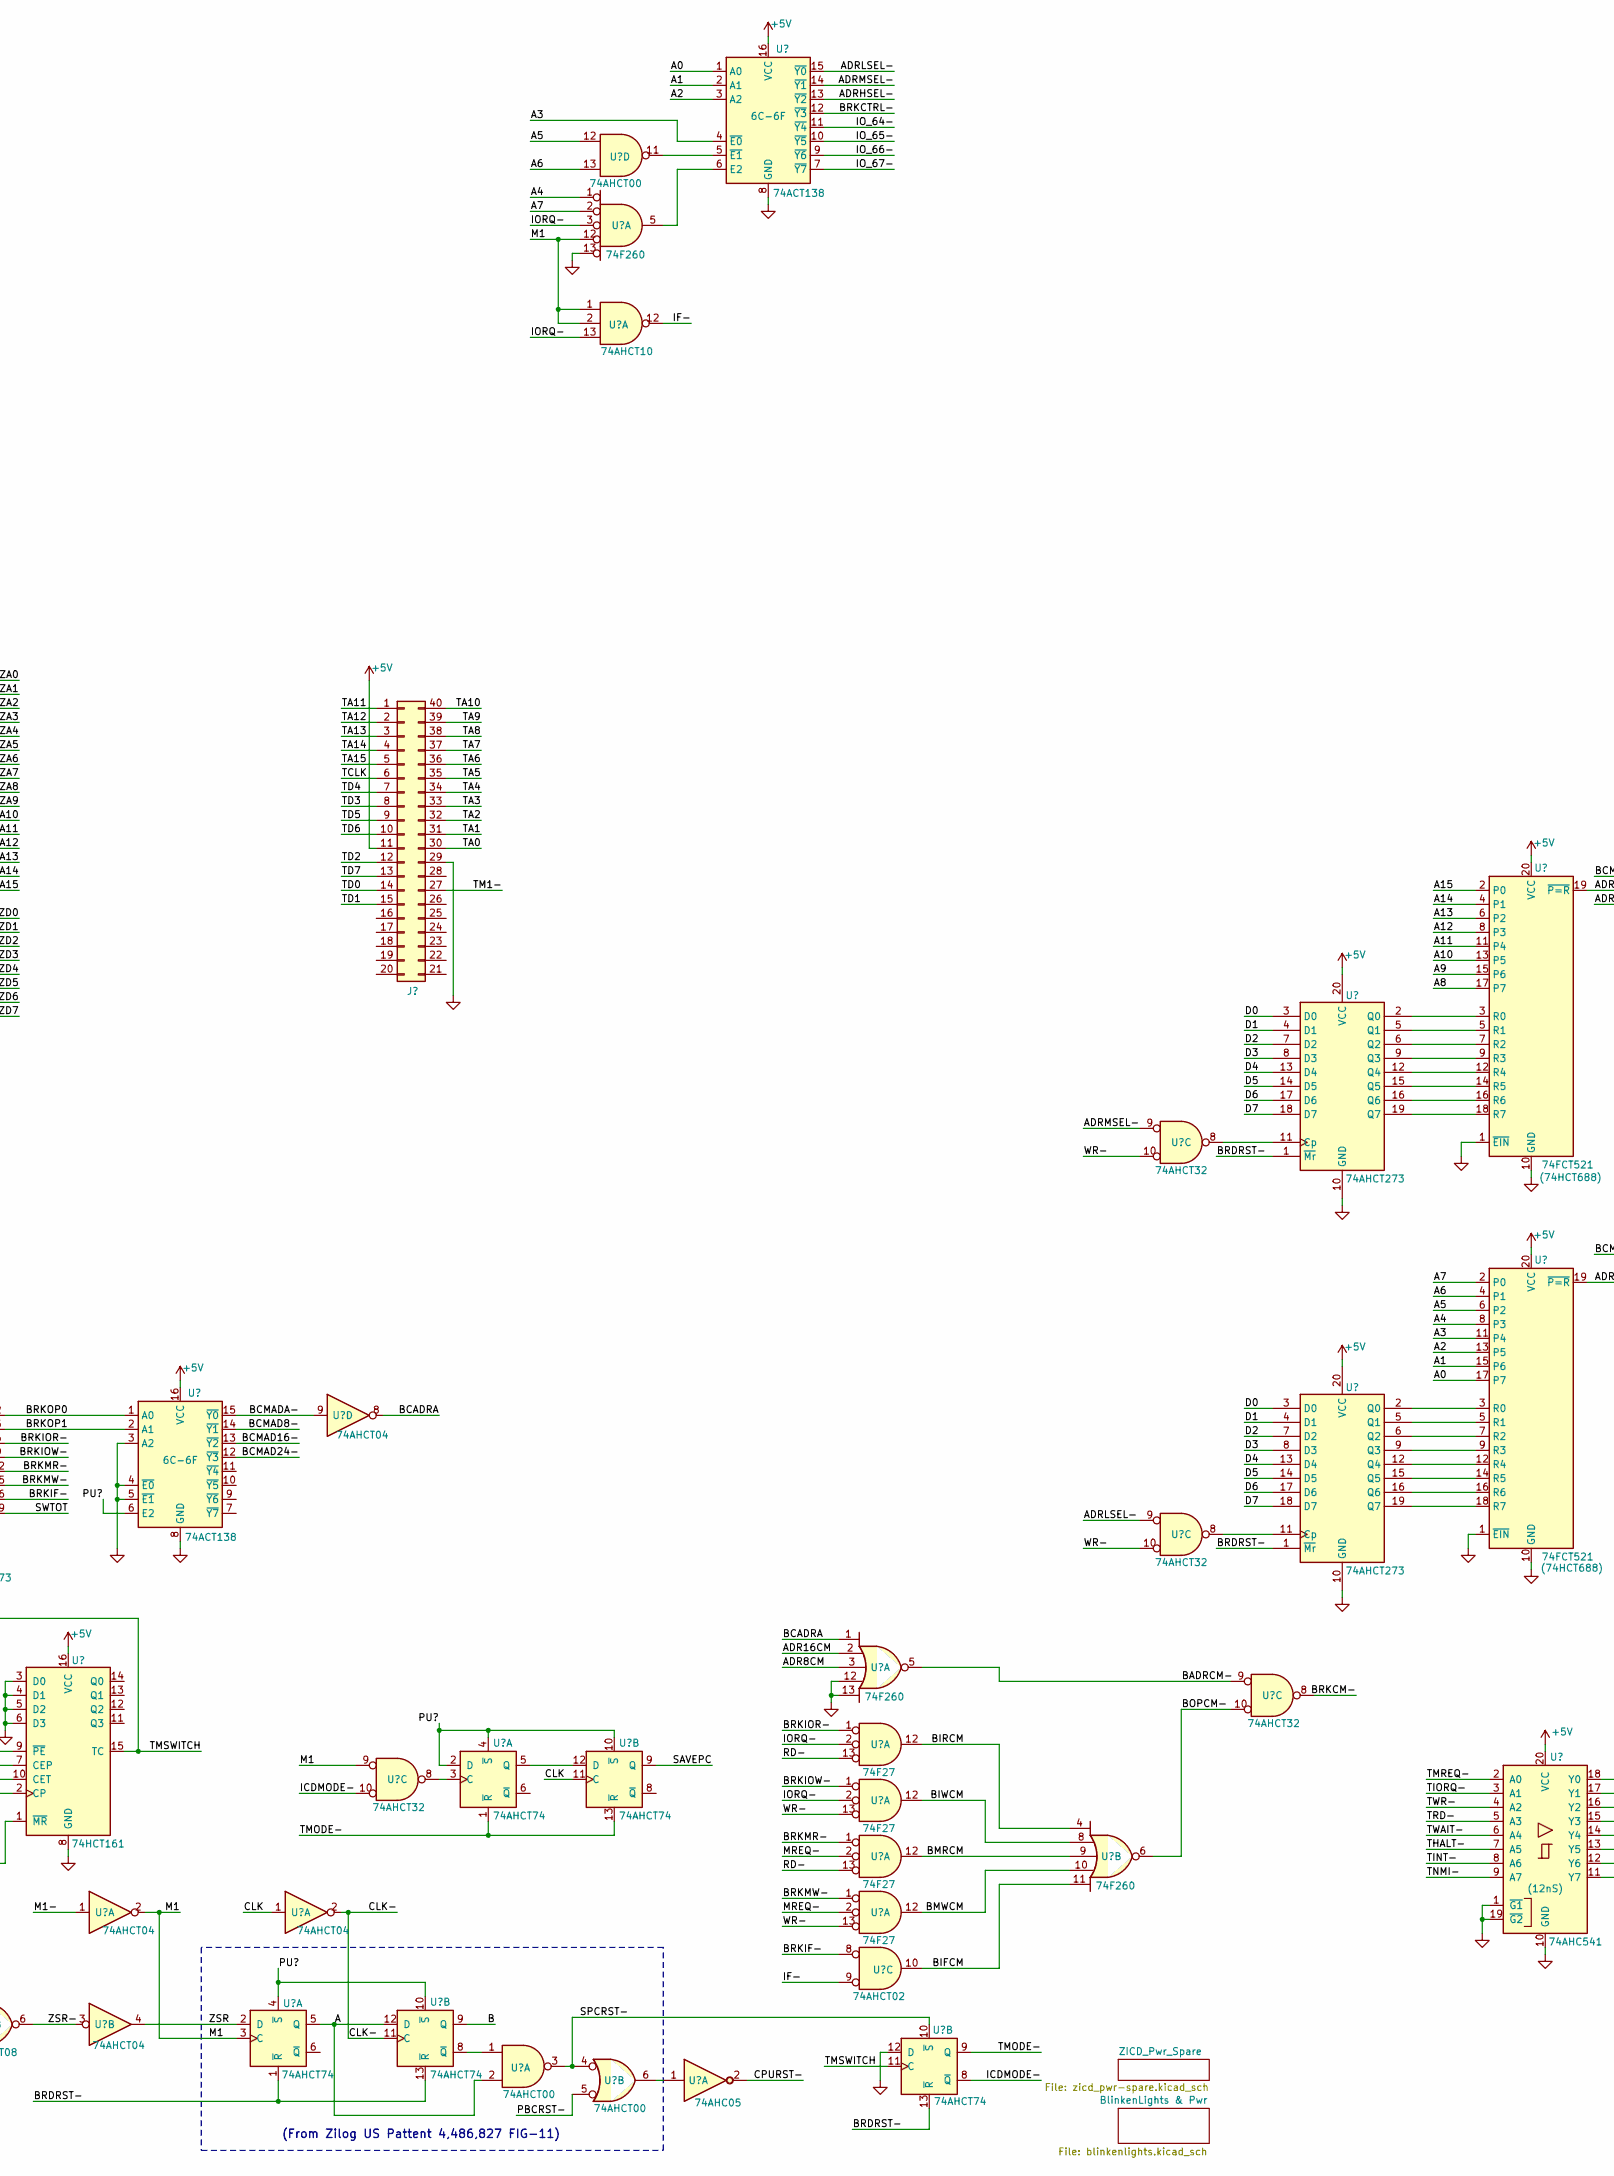
[picture p41: schematic sd-zicd.kicad_sch, part in row 1, column 2]

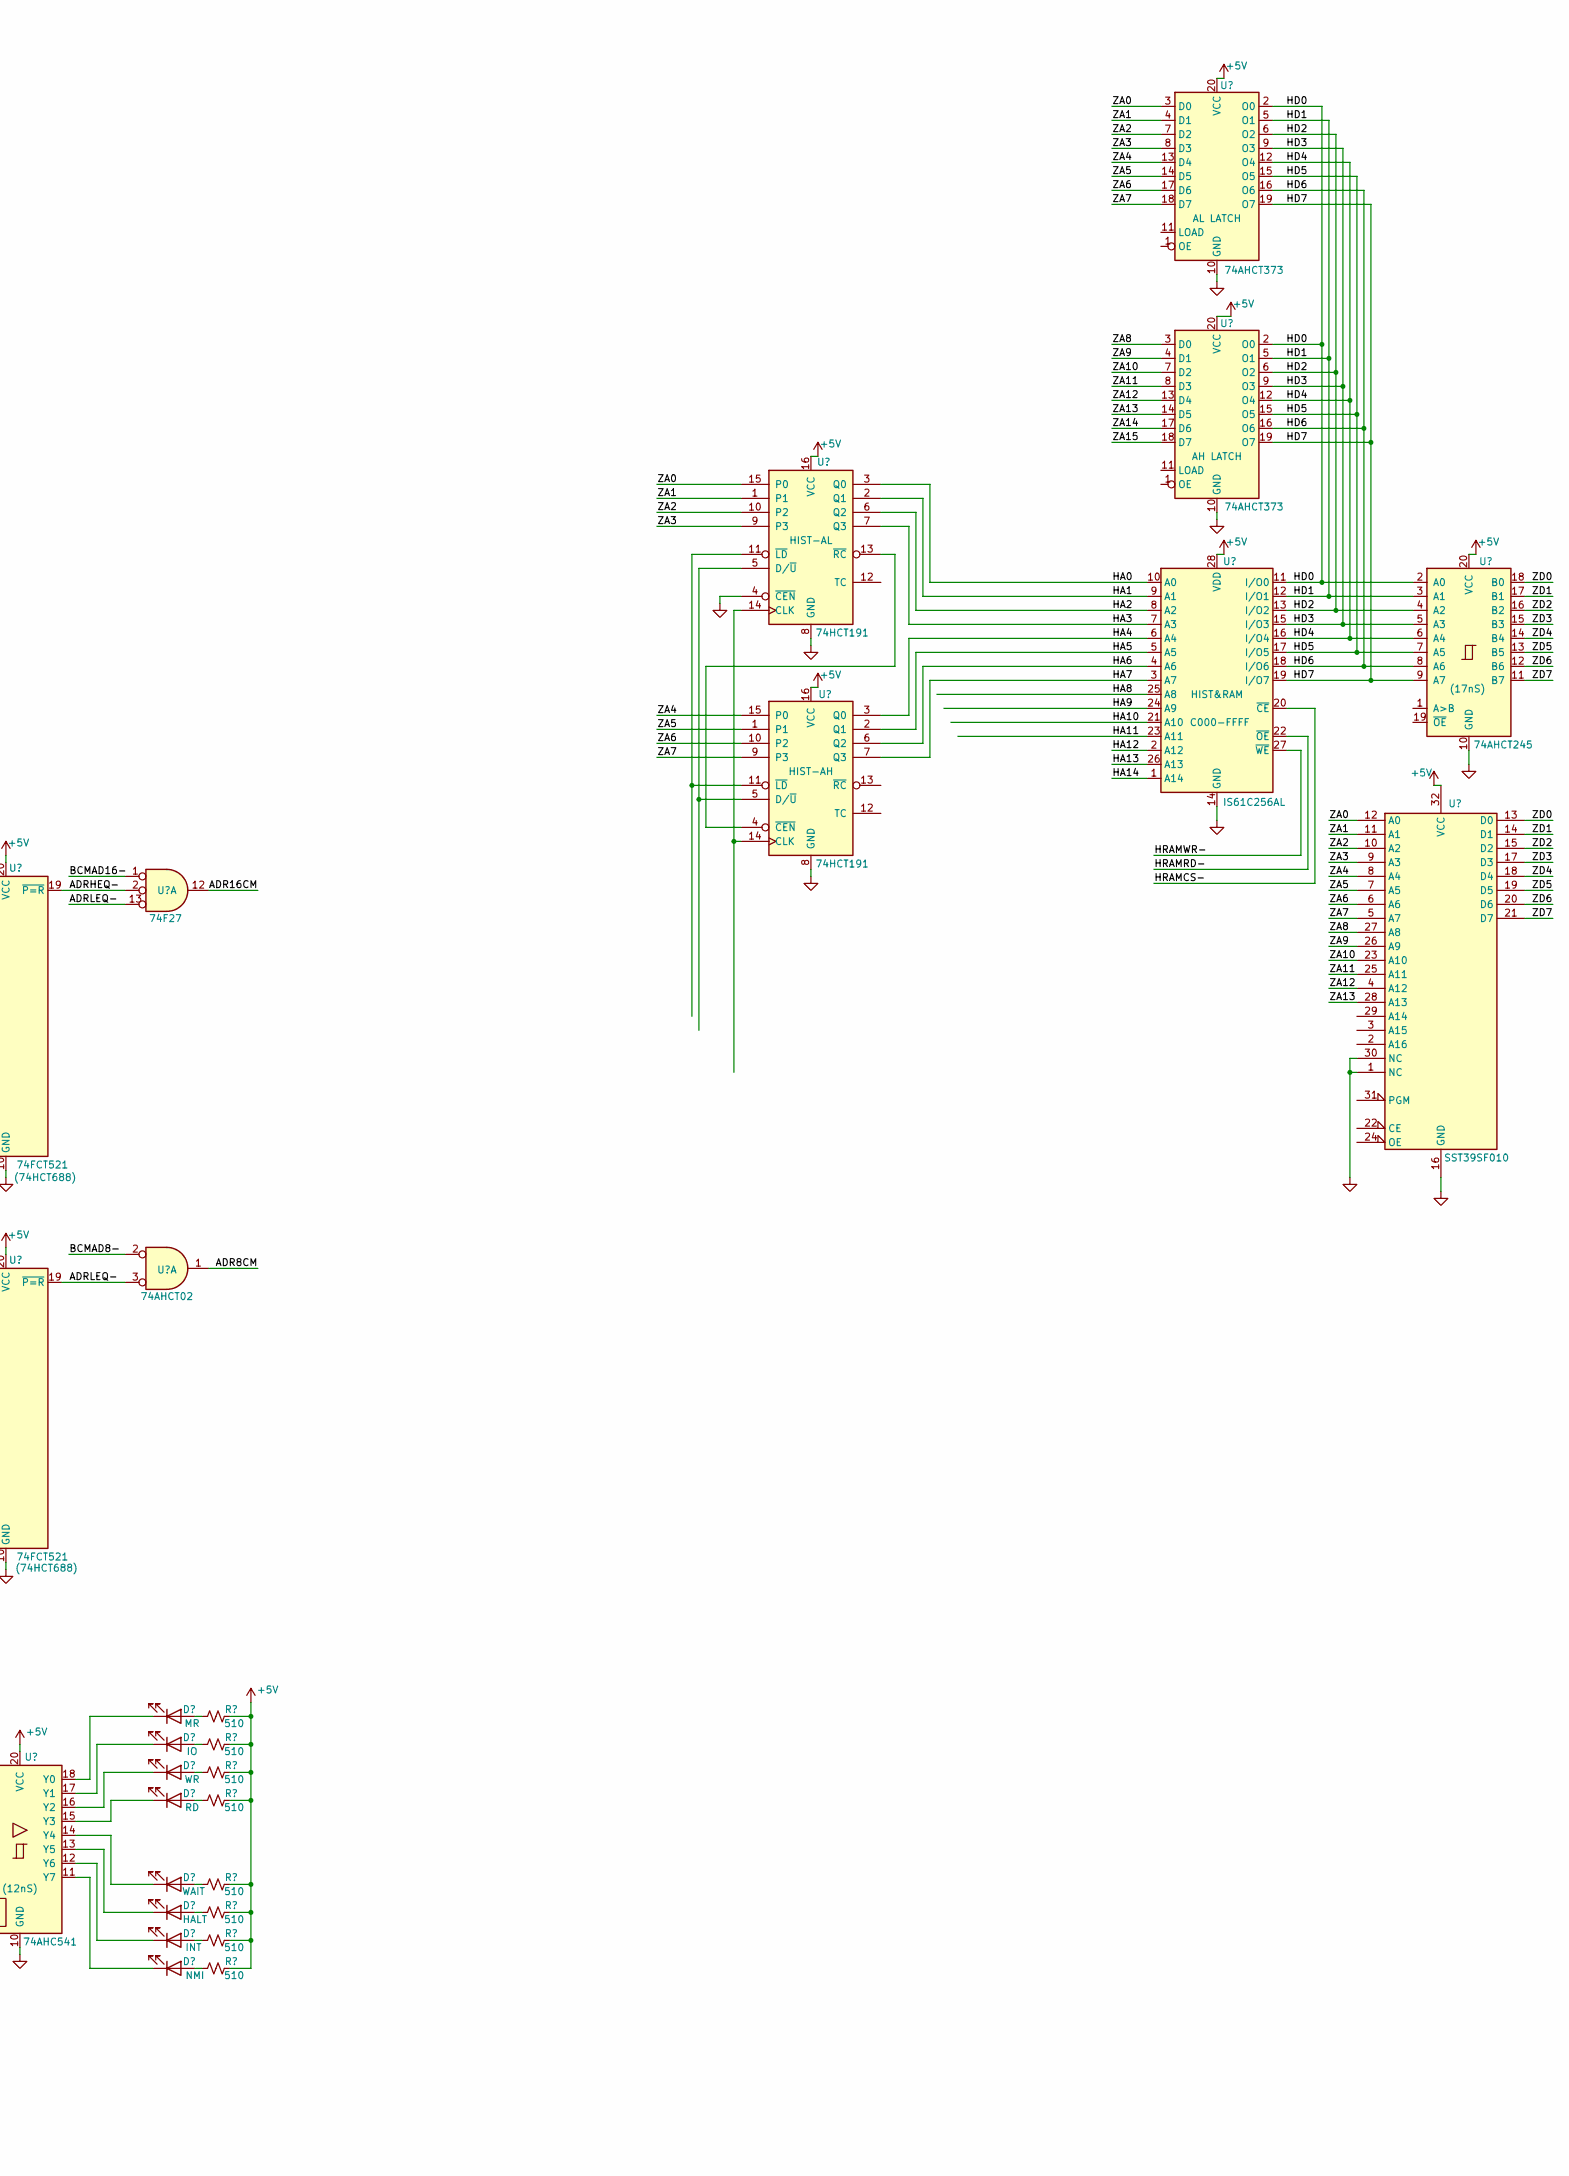
[picture p42: schematic sd-zicd.kicad_sch, part in row 1, column 3]

Parts:
D6: PMEG2010AEB; D_SOD-323_HandSoldering
R23: 20k; R_0805_2012Metric
U33: 74LVC1G06W; SOT-23-5
U36: SN74LVC8T245NS; SO-24_5.3x15mm_P1.27mm
U37: 74LVC125AS; SOIC-14_3.9x8.7mm_P1.27mm
U43: 74AHCT1G02; SOT-23-5

Connections:
+3.3V: R23.1, U36.23 (V_{CCB}), U36.24 (V_{CCB}), U37.14 (VCC)
+5V: D6.2 (A), U33.5 (VCC), U36.1 (V_{CCA}), U43.5 (VCC)
GND: U33.3 (GND), U36.11 (GND), U36.12 (GND), U36.13 (GND), U37.1, U37.7 (GND), U43.3 (GND)
IMSEL3-: U37.3
IMSEL-: U37.2, U43.2
IRD-: U36.2 (A>B)
WAIT: U33.2, U43.4
WAITRQ-: R23.2, U43.1
ZD0: U36.3 (A1)
ZD1: U36.4 (A2)
ZD2: U36.5 (A3)
ZD3: U36.6 (A4)
ZD4: U36.7 (A5)
ZD5: U36.8 (A6)
ZD6: U36.9 (A7)
ZD7: U36.10 (A8)
ZWAIT-: U33.4

Notes on the sheet:
3.3V Logic Section
(From Zilog US Pattent 4,486,827 FIG-11)
